AStoker/sound-machine/3d-print/enclosure-wiring.png

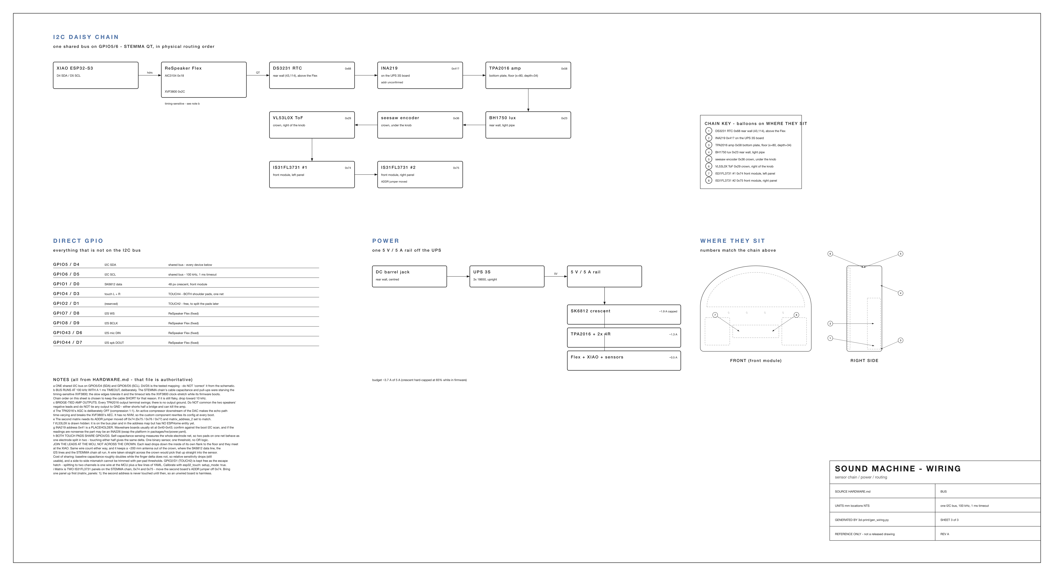
3d-print/enclosure-wiring.png
