AStoker/sound-machine/3d-print/models/backpack-mount-study.png

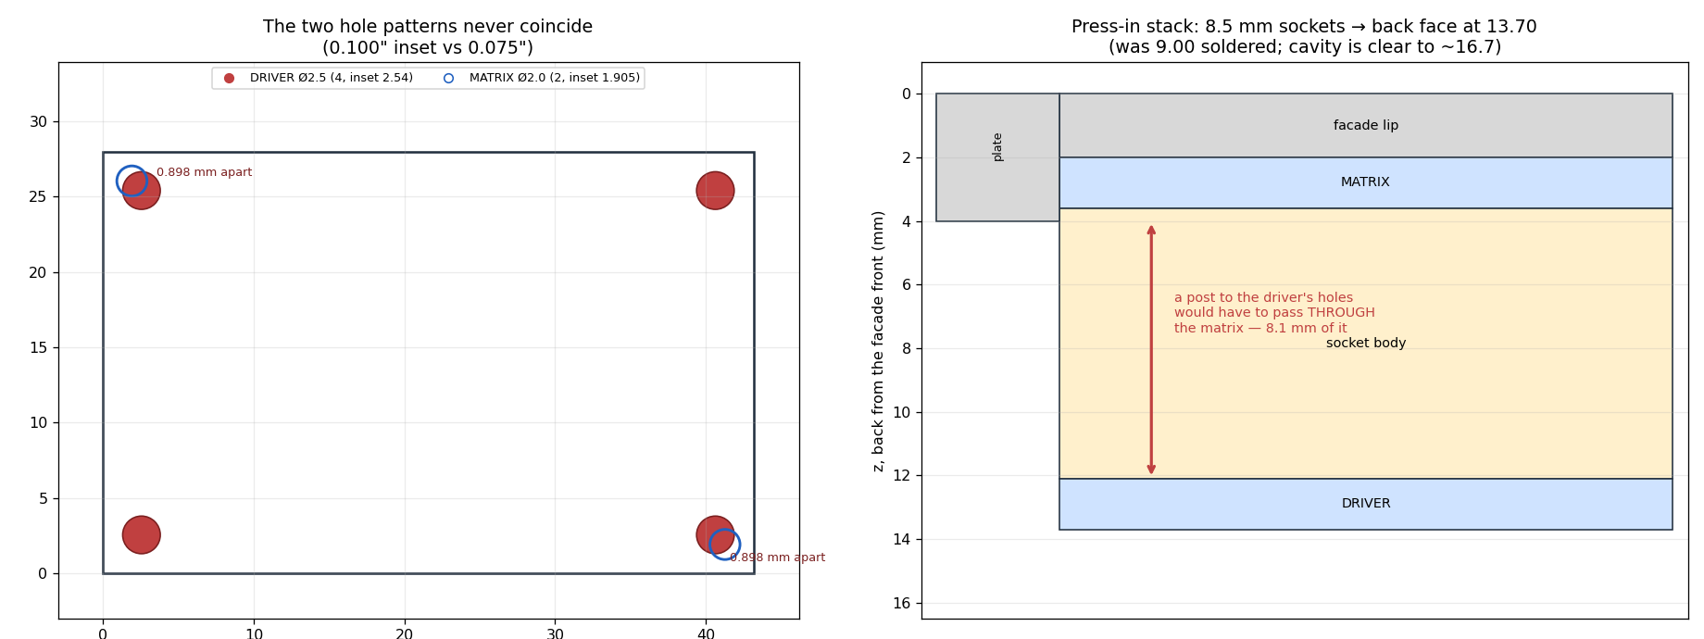
3d-print/models/backpack-mount-study.png
