AStoker/sound-machine/3d-print/models/bottom-plate-check.png

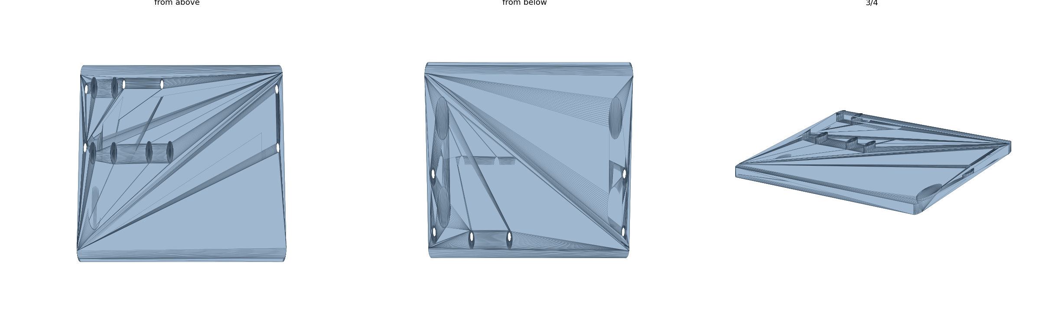
3d-print/models/bottom-plate-check.png
