AStoker/sound-machine/3d-print/models/matrix-mount.png

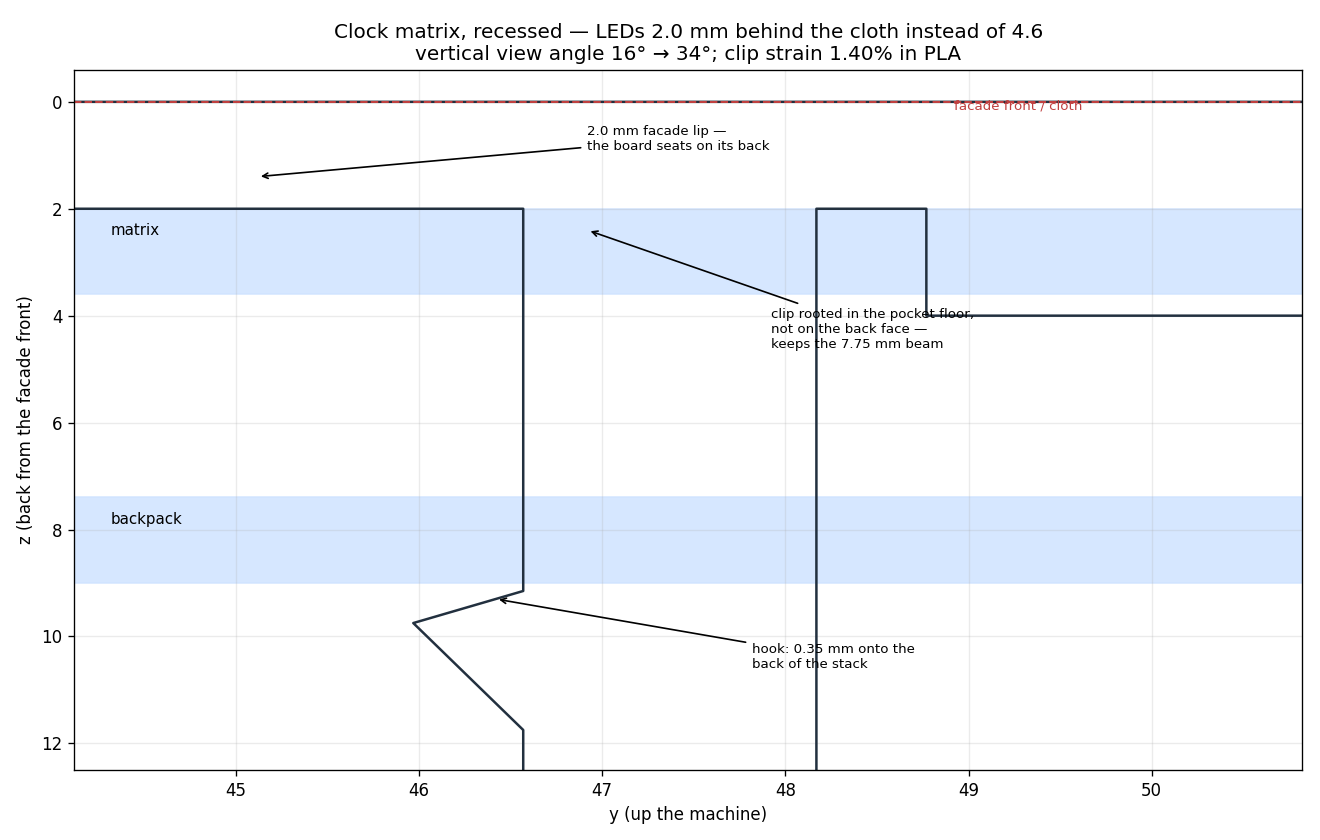
3d-print/models/matrix-mount.png
