AStoker/sound-machine/3d-print/tray_sections.png

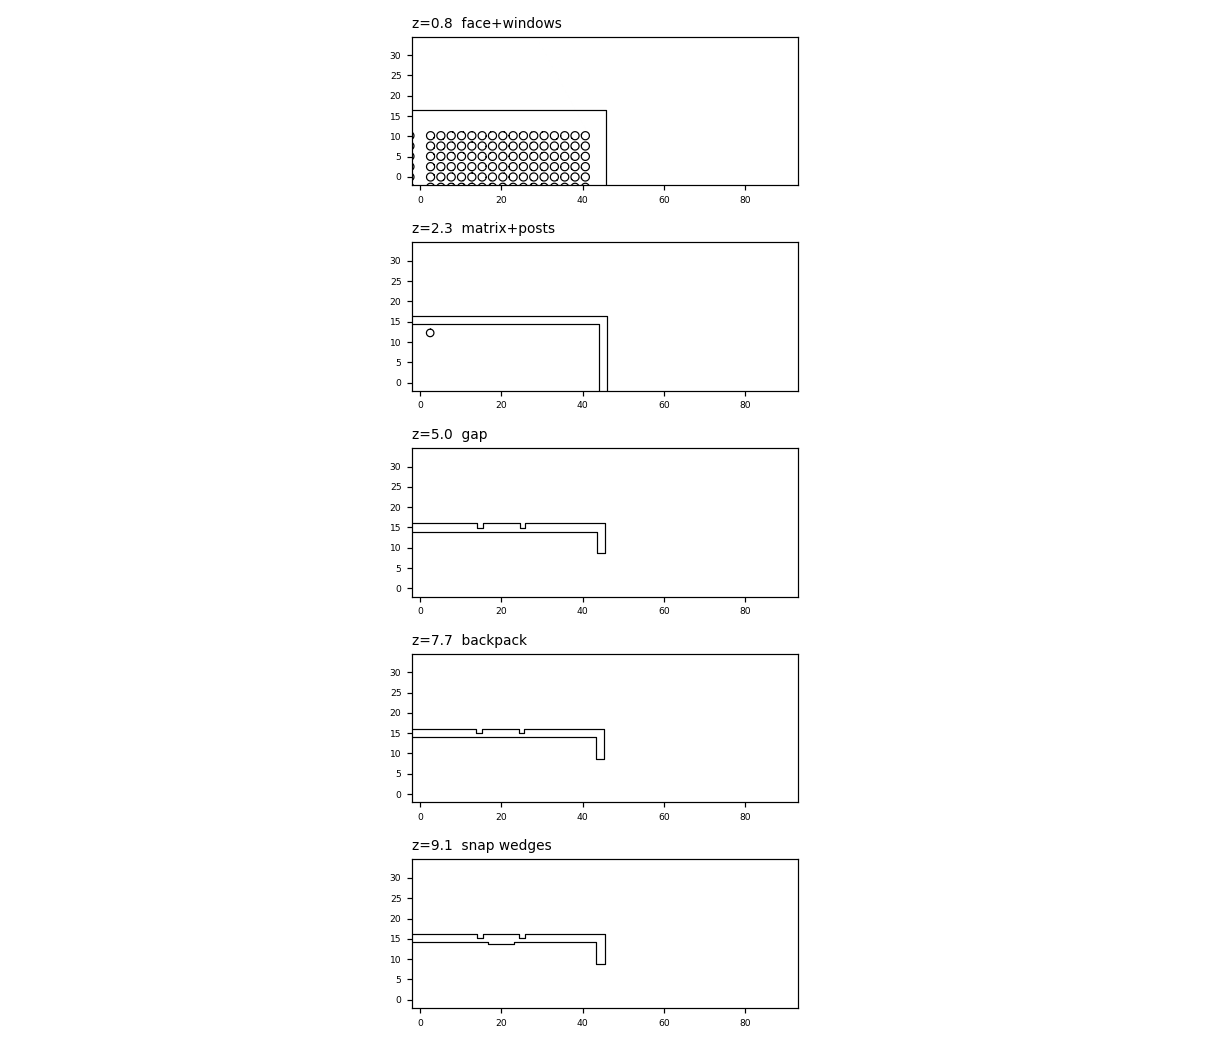
3d-print/tray_sections.png
