AStoker/sound-machine/3d-print/models/matrix-testfit.png

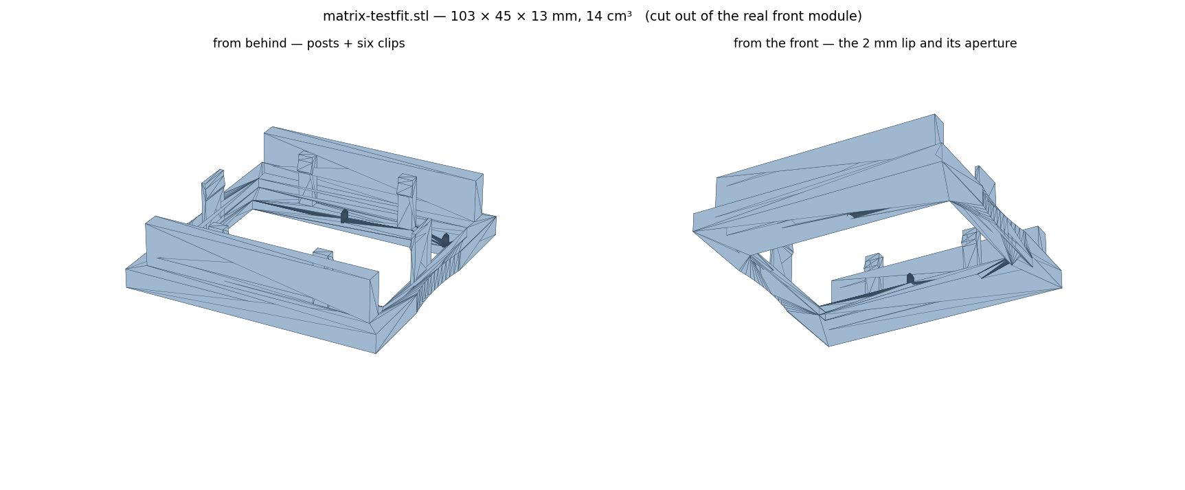
3d-print/models/matrix-testfit.png
