AStoker/sound-machine/3d-print/models/dome-changes.png

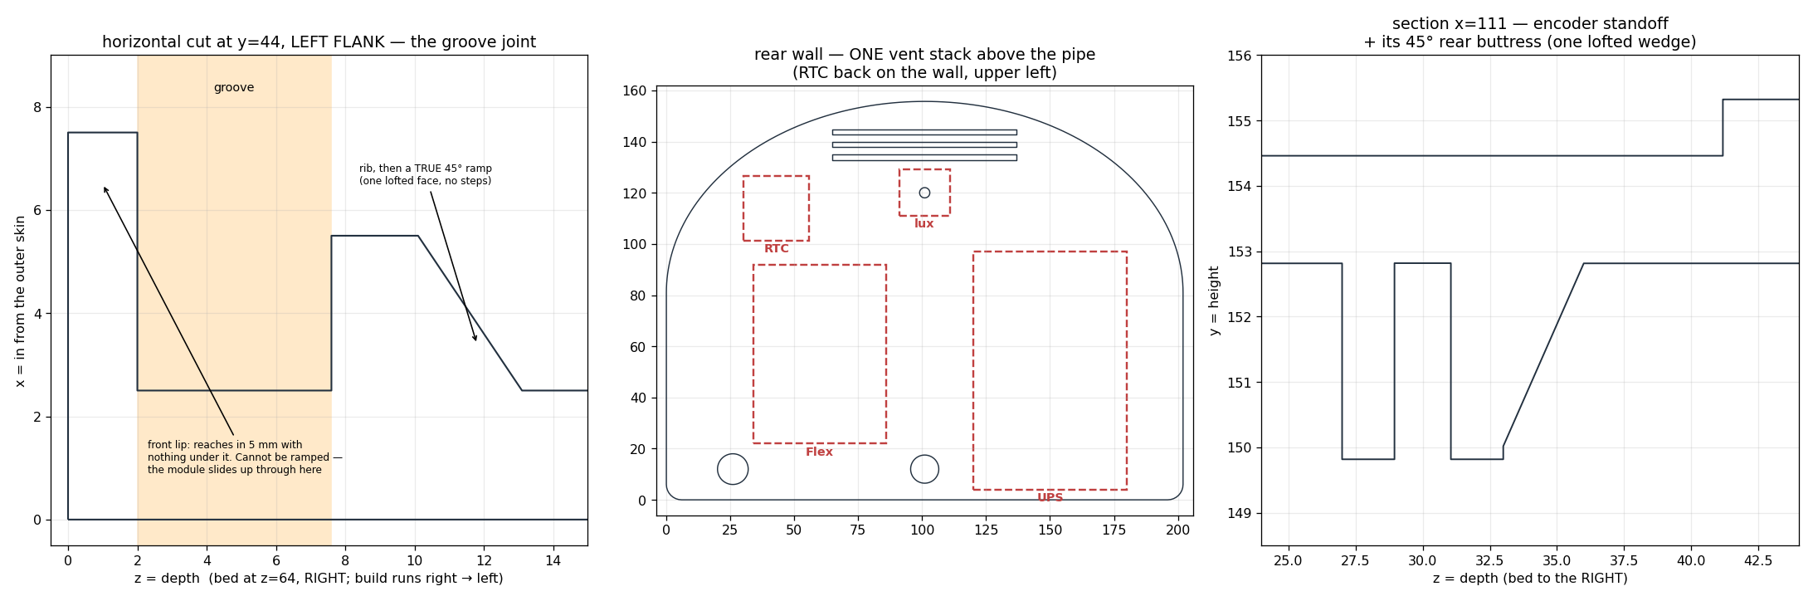
3d-print/models/dome-changes.png
