AStoker/sound-machine/3d-print/models/front-plate-changes.png

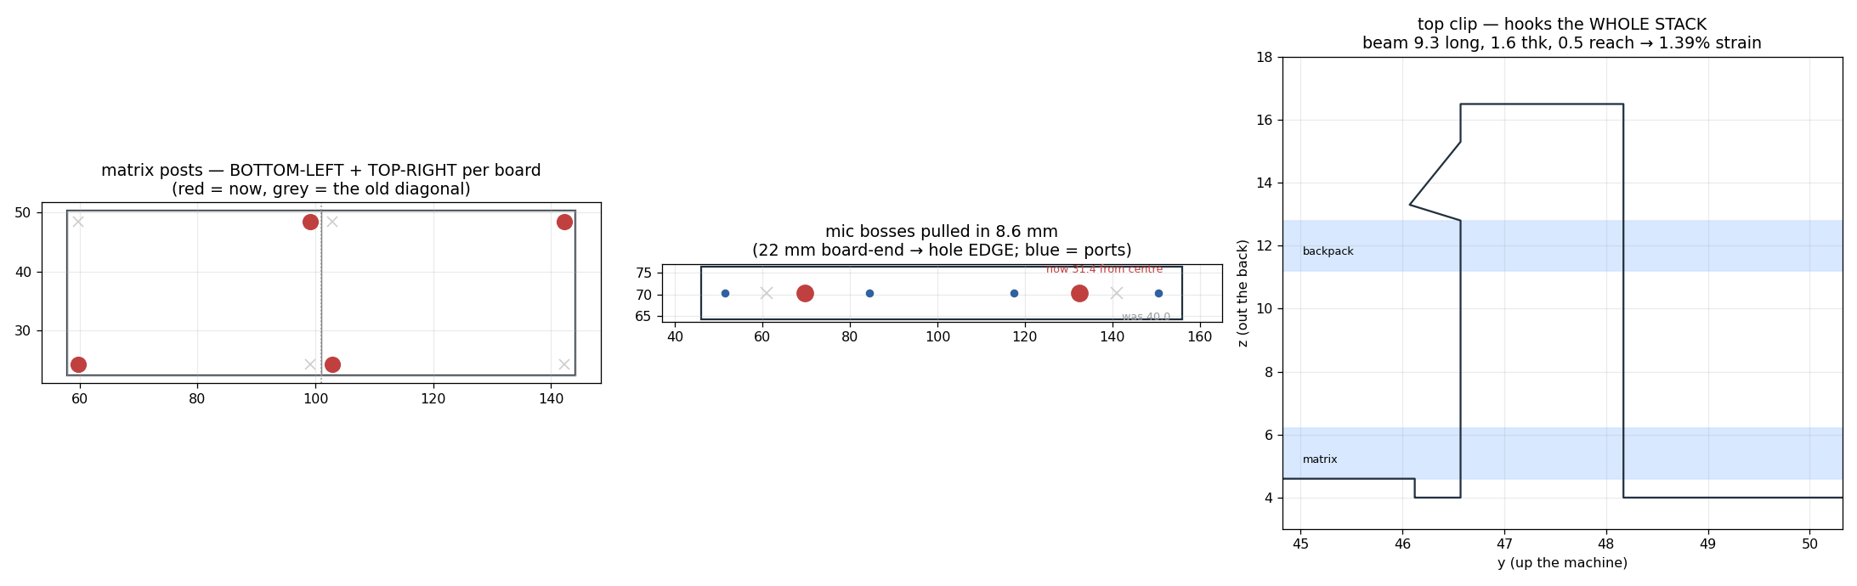
3d-print/models/front-plate-changes.png
