AStoker/sound-machine/packages/settings.yaml

# =====================================================================
# SETTINGS - every tunable in the build, in one file
#
# This package contains NOTHING BUT `substitutions:`. It is the single place to
# change a value; no package below it hardcodes a number you might want to edit.
# It is split out of soundmachine.yaml so the entry file can stay a short,
# readable device core.
#
# HOW THESE ARE OVERRIDDEN. Local substitutions beat package ones, so the tiny
# device YAML on Home Assistant (soundmachine.min.yaml) can override any value
# here - that is how credentials get injected without `!secret` ever appearing in
# this repo (remote ESPHome packages forbid `!secret`).
#
# SECTIONS, in the order the packages that read them are loaded:
#   1. Device identity + credentials
#   2. Buses and pins (I2C addresses, I2S, GPIO)
#   3. Ambient light (the shared auto-dim level)
#   4. Display service (content channels, clock, message widths)
#   5. Clock display (the LED matrix panels)
#   6. Audio chain (amp, noise, volume, ducking, voice)
#   7. Crescent light (strip, presets, sunrise, alarm)
#   8. Knob indicator + proximity
#   9. Power / UPS monitoring
#  10. Gestures (shared tap/hold timings)
#  11. Media sources
#  12. Logging
#
# CONVENTION: a value that is DERIVED from something else (the LED row layout,
# the display panels' register map) is NOT a substitution - it lives next to the
# code that owns it, so nobody is tempted to "tune" it. See the crescent note in
# CLAUDE.md for the one geometry coupling that is enforced by a script.
# =====================================================================
substitutions:

  # ===================================================================
  # 1. DEVICE IDENTITY + CREDENTIALS
  # ===================================================================
  device_name: soundmachine
  device_friendly_name: Sound Machine
  ap_ssid: "Soundmachine Setup"

  # ---- Credentials (injected, NOT stored here) ----
  # This config is designed to be pulled as a remote ESPHome package, and remote
  # packages may not contain `!secret` lookups. So credentials are substitutions
  # instead: the local device YAML on Home Assistant overrides each of these with
  # `!secret ...` from its own secrets.yaml (a local substitution wins over the
  # package's). The values below are PLACEHOLDERS - a real build must override
  # them. See soundmachine.min.yaml / secrets.example.yaml.
  wifi_ssid: "set-in-local-secrets"
  wifi_password: "set-in-local-secrets"
  ap_password: "set-in-local-secrets"
  ota_password: "set-in-local-secrets"
  # Must be a valid 32-byte base64 key or even a bare `esphome config` fails
  # format validation before the local override lands. This is a throwaway key.
  api_key: "kreOUJQZbPUFn1efUReXwEbfhkZzuGGXk1t2AKESiVs="

  # ===================================================================
  # 2. BUSES AND PINS
  # HARDWARE.md holds the authoritative map and the wiring cautions; these are
  # the values the firmware actually uses.
  # ===================================================================

  # ---- I2C: ONE bus, everything hangs off it ----
  pin_i2c_sda: GPIO5                 # D4 on the XIAO/Flex breakout
  pin_i2c_scl: GPIO6                 # D5
  # 100 kHz, not the 400 kHz default: slower edges tolerate the extra cable
  # capacitance and pull-ups of the STEMMA sensor chain, which was starving the
  # timing-sensitive XVF3800. If it is still flaky with everything reconnected,
  # try 10kHz. EVERY package that adds I2C traffic is written to respect how
  # narrow this bus is - see the knob indicator and the display dedup.
  i2c_frequency: 100kHz
  # Room for the XVF3800 to clock-stretch while its firmware boots; without it
  # setup logs "I2C transaction timeout".
  i2c_timeout: 1ms

  # ---- I2C addresses (no conflicts; confirm against the boot scan) ----
  i2c_addr_codec: "0x18"             # AIC3104 codec on the Flex
  i2c_addr_ambient_light: "0x23"     # BH1750
  i2c_addr_tof: "0x29"               # VL53L0X
  i2c_addr_xvf3800: "0x2C"           # ReSpeaker XVF3800 voice front-end
  i2c_addr_knob: "0x36"              # rotary encoder + its NeoPixel
  i2c_addr_amp: "0x58"               # TPA2016 amplifier
  i2c_addr_rtc: "0x68"               # DS3231 real-time clock

  # ---- I2S (pins fixed by the Flex's internal routing - do not change) ----
  pin_i2s_ws: GPIO7                  # D8, LRCLK
  pin_i2s_bclk: GPIO8                # D9
  pin_i2s_din: GPIO43                # D6, mic data in
  pin_i2s_dout: GPIO44               # D7, speaker data out

  # ---- Remaining GPIO ----
  pin_crescent_data: GPIO1           # D0, SK6812 data. Verify D0 is exposed and
                                     # unused on the Flex breakout pads.
  touch_pin: GPIO4                   # capacitive preset pad (D3; D2 = GPIO3).
                                     # ESP32-S3 touch channels are GPIO1..14.

  # ===================================================================
  # 3. AMBIENT LIGHT - the shared auto-dim level
  # The BH1750 produces ONE abstract level, 0..15 (`ambient_level`), consumed by
  # both the display service and the knob indicator. Deliberately weighted dark:
  # the level sits at the floor for anything up to a dim room and only climbs
  # into the top half in real daylight, because this device is 60cm from a face
  # at 3am.
  # ===================================================================
  ambient_update_interval: 5s
  ambient_lux_dark: "3"              # at/below this lux -> ambient_level_min
  ambient_lux_bright: "500"          # at/above this lux -> ambient_level_max
  ambient_level_min: "0"             # floor of the scale; the matrix maps this
                                     # onto matrix_pwm_min, never to fully dark
  ambient_level_max: "14"
  # Curve shape between the two anchors. >1 holds the low end down; 1.0 would be
  # a straight log ramp, which leaves an ordinary lamp-lit room too bright.
  ambient_dim_gamma: "1.8"
  # Per-reading slew toward the target level (0..1). Stops a visible step when
  # someone walks past the sensor. 1.0 = snap.
  ambient_slew: "0.35"

  # ===================================================================
  # 4. DISPLAY SERVICE (packages/api/display.yaml)
  # What gets SHOWN and for how long. How it is drawn is section 5.
  # ===================================================================
  # One heartbeat drives everything the display does: expiring timed overlays,
  # advancing a scroll, and picking up the minute rolling over. It is safe to
  # tick this fast because the driver skips the I2C write when the resolved frame
  # is unchanged - an idle tick costs building a small struct and comparing it.
  display_tick_ms: "250"
  clock_24h_mode: "false"            # true = 24h; the leading zero is blanked
                                     # either way

  # How long a transient CODE ("L1", "S3", "OFF", a volume percentage) stays up.
  display_code_seconds: "2"

  # ---- KEEP THE STRINGS BELOW TO 4 CHARACTERS ----
  # 4 is how many glyphs fit on this display without one of them landing on the
  # dead column between the two panels, so 4 characters is what SITS STILL.
  # Longer strings still work, they just scroll - and a scrolling pass takes far
  # longer than the few seconds one of these is meant to occupy. The budget is the
  # same for every channel, because every channel is drawn the same way; the
  # slot layout is explained in components/clock_display/clock_display.h under
  # "STATIC TEXT NEVER TOUCHES THE SEAM".
  #
  # Power-source announcements, raised when External Power flips (charger in or
  # out). Gated on the averaging window plus ups_confirm_time, so the message
  # lands up to ~90s after the plug moves, not instantly - that lag is what
  # stops a full pack's idle current excursions announcing a false mains loss.
  power_msg_mains: "CHG"
  power_msg_battery: "BATT"
  power_msg_seconds: "3"
  # The sticky low-battery alert. It is a DEFAULT VIEW, not an interruption: it
  # stands in for the clock while the pack is low and anything transient - a
  # volume readout, a preset code, "CHG" - still shows over the top of it.
  # Short and STATIC on purpose: this one persists for as long as the pack is
  # low, and a permanently scrolling word at a bedside at night is worse than no
  # warning at all.
  alert_msg_low_battery: "LOW"

  # ---- Home Assistant authored message (packages/behavior/message.yaml) ----
  display_message_duration_default: "20"  # seconds the custom text stays up
  display_message_duration_min: "3"
  display_message_duration_max: "300"
  # Horizontal scroll rate, used for any text too wide for its channel's budget.
  display_scroll_ms_per_px_default: "250"  # lower = faster
  display_scroll_ms_per_px_min: "30"
  display_scroll_ms_per_px_max: "1000"
  display_scroll_ms_per_px_step: "10"

  # ===================================================================
  # 5. CLOCK DISPLAY - the tiled 16x9 LED matrix panels
  # ===================================================================
  # The panel addresses, left to right. HOW MANY PANELS THERE ARE is not a
  # setting: it is the length of the `addresses:` list in hw/matrix.yaml, so
  # there is nothing here that could disagree with it. To bring up the left panel
  # alone, delete the second entry from that list - the other address is then
  # never touched, so an unwired board causes no I2C errors.
  matrix_address: "0x74"             # panel 0 (left)
  matrix_address_2: "0x75"           # panel 1 (right); set the 2nd board's ADDR
                                     # jumper to a free address (0x75/76/77)
  # Physical dead columns between adjacent panels. Two panels butted together
  # are NOT seamless; the driver lays content out in physical columns that
  # include this gap and maps back to logical columns at draw time.
  matrix_panel_gap: "1"
  matrix_pwm_on: "40"                # lit-pixel PWM at full ambient (0..255)
  matrix_pwm_min: "3"                # lit-pixel PWM floor at the darkest end.
                                     # Never 0 - digits must stay readable.
  # How often the driver checks that the panels still hold the configuration it
  # wrote them. The panels have no NVM, so a glitch on the 5V rail returns them
  # to their power-on state - blanked, with every LED disabled - and they would then
  # sit dark forever while the driver happily kept pushing PWM at them. The probe
  # is a 1-byte register read per panel, so this is cheap to run often; the
  # ceiling on how long a reset display could stay dark is this interval.
  matrix_probe_interval: 10s

  # ===================================================================
  # 6. AUDIO CHAIN
  # ===================================================================
  # The audio stack is not safe to drive until well after setup: starting the
  # noise generator during setup dereferenced an uninitialized event group and
  # crashed. api/sound.yaml waits this long at boot priority -100, then raises
  # on_audio_ready.
  audio_ready_delay: 2s

  # ---- Speaker amplifier ----
  # gain_db is the CEILING, not the operating point - volume lives in the
  # AIC3104 upstream. Was 6 dB (~1W full-scale); raised to 9 dB (~2W) because
  # the mix was a touch quiet. That is near the physical ceiling of a 5V/4-ohm
  # amp (the limiter parks at ~2.5W), so there is little clean headroom left.
  # Going much past 9 pushes normal peaks into the limiter, which distorts AND
  # makes the DAC->speaker path non-linear again - the exact thing running with
  # AGC off is protecting for the XVF3800's echo canceller. If you hear it clip
  # or "breathe" before the knob maxes out, come back down.
  # NOT the lever for the constant speaker hiss - that is the codec's own
  # converter noise, upstream of this gain, so turning it down attenuates hiss
  # and signal equally. Diagnosis and the real options are in
  # FUTURE-DEVELOPMENT T6.
  amp_gain_db: "9"
  # 9.0 dBV is the top of the range (~2.5W into 4 ohm), just under the clipping
  # point at 5V. It should NEVER engage in normal use - it is a fault stop, not
  # a dynamics tool.
  amp_limiter_dbv: "9.0"
  # How often the amp's registers are re-written. The amp has no NVM, so a glitch
  # on the 5V rail returns it to factory defaults - AGC back ON, which quietly
  # breaks the XVF3800's echo canceller and has no other symptom. Four verified
  # register writes, so this is affordable to repeat; the interval is the longest
  # the device could run mis-configured.
  amp_reassert_interval: 60s

  # ---- Noise generator ----
  noise_gain: "30%"                  # base amplitude; leaves headroom so noise
                                     # plus a TTS reply cannot clip
  noise_fade_length: "2s"
  noise_high_pass_hz: "160"
  noise_high_pass_makeup: "4.0"      # tune by ear against white at one volume

  # ---- Sampled ambiences (La La and Crickets; packages/hw/audio_chain.yaml) ----
  # These apply to ALL of them - the component holds one gain and one fade for the
  # whole list, because per-file levelling belongs in the files. 100% because each
  # FILE already carries its own level (see section 11), and at unity the
  # component passes decoded frames through untouched. Re-encode rather than
  # turning this down: the peak headroom the mixer and a TTS reply need was
  # chosen per file, and one gain here cannot respect two different ceilings.
  ambience_gain: "100%"
  # Applied when an ambience starts, and when one is switched for another. Shorter
  # than the noise fade because there is no cold filter state to ease in - the
  # first sample is already the right sound. There is deliberately NO fade at the
  # loop point.
  ambience_fade_length: "1s"

  # ---- Volume ----
  #
  # THE VOLUME FRACTION IS LINEAR IN DECIBELS, WHICH IS WHY THESE NUMBERS LOOK
  # THE WAY THEY DO. Follow one knob click through the chain: the media player
  # remaps its 0..1 volume into [volume_floor_pct, volume_ceiling_pct], hands
  # that to the mixer, which hands it to the AIC3104, whose DAC volume register
  # is 128 steps of 0.5 dB (0x00 = 0 dB, 0x7F = -63.5 dB, 0x80 = mute). So
  #
  #     attenuation = 64 dB x (1 - floor) x (1 - knob)
  #
  # and the knob fraction is already a perceptual scale - equal fractions of the
  # knob are equal decibels. Two things follow, and both were wrong before:
  #   * The FLOOR sets how quiet the machine can get, in dB, and nothing else
  #     does. At the old 55% the bottom of the knob was only -28.8 dB, which is
  #     a bedroom-at-2am kind of loud for a hot recording like Crickets.
  #   * A step curve that is COARSE at the bottom (the old one, ~9% per click
  #     there) spends 2.6 dB on a click at exactly the level where you are
  #     trying to place a whisper. Fine steps belong at the quiet end.
  volume_floor_pct: "30%"            # media_player volume_min. Bottom of the
                                     # knob = -44.8 dB, i.e. 16 dB quieter than
                                     # the old 55%; a true whisper is reachable.
                                     # Knob EXACTLY 0 still mutes the codec
                                     # outright (media player mutes below 0.001),
                                     # which is also the one setting with no hiss
                                     # (FUTURE-DEVELOPMENT T6).
                                     # LOWER STILL IS NOT FREE: the codec's hiss
                                     # does not scale with volume, so every dB of
                                     # extra range makes it relatively louder at
                                     # the bottom. If the quiet end sounds hissy
                                     # rather than quiet, come back up, don't
                                     # chase it with amp_gain_db.
  volume_ceiling_pct: "100%"
  # Knob step curve, interpolated across the knob's travel:
  #     step = at_zero + (at_full - at_zero) x volume
  # FINE WHEN QUIET, coarse when loud - the opposite of what was here before,
  # because the fraction is decibels (above) and the quiet end is the end that
  # gets used. ~1.1 dB per click near the bottom, ~2.7 dB near the top, and
  # ~25 clicks for the full sweep - close to the ~21 it used to take, so the
  # knob has not become a longer journey, only a better-placed one.
  volume_step_at_zero: "0.025"
  volume_step_at_full: "0.06"

  # ---- Voice assistant + ducking ----
  wake_word_model: okay_nabu
  # 0.9, down from the 0.97 default: a bit more forgiving, especially once
  # background sound resumes after a turn.
  wake_word_cutoff: "0.9"
  mic_mute_update_interval: 60s      # was 1s - quieter logs, still functional
  duck_decibels: "15"                # dip applied to background sound for a turn
  # In MILLISECONDS, not a time period: these are passed as script parameters
  # (see sound_duck_apply in api/sound.yaml, which writes the channel list once
  # rather than once per depth), and a script parameter is a plain int.
  duck_ramp_ms: "300"                # ramp INTO the dip
  unduck_ramp_ms: "500"              # ramp back out - gentler, so the background
                                     # does not swell after a reply
  # The duck watchdog waits for the spoken reply to start, then to finish. Both
  # waits are bounded so a stuck announcement state cannot leave sound ducked
  # forever.
  duck_reply_start_timeout: 10s
  duck_reply_end_timeout: 30s

  # ===================================================================
  # 7. CRESCENT LIGHT - SK6812 strip, presets, sunrise, alarm
  # NOTE: the pixel COUNT and row layout are NOT here. They are derived from the
  # enclosure geometry and live in packages/hw/crescent.yaml, checked by
  # 3d-print/check_docs.py. See the coupling note in CLAUDE.md.
  # ===================================================================
  # Gamma 1.0 = linear brightness, so low values still light. SK6812s otherwise
  # blank out below ~20% at the default 2.8 gamma. Raise toward 2.8 for a more
  # perceptual fade, at the cost of the dim end.
  led_gamma: "1.0"
  # Hard current ceiling, as a % of full-white output. Caps max PWM
  # (color_correct) so the strip PHYSICALLY cannot exceed it whatever HA asks.
  # BUDGET (5V rail = Waveshare UPS 3S, 5A):
  #   48 SK6812 RGBW at full all-channel white ~= 2.9A
  #   Speaker amp into 2x 4ohm at clipping           ~= 1.3A
  #   Flex + XVF3800 + ESP32-S3 + sensors        ~= 0.5A
  # STOPGAP: 65% (~1.9A, ~3.7A of 5A total on paper) was enough to brown out the
  # ESP32 in practice - the strip latches its last frame independent of the MCU,
  # so once the rail sags enough to reset the ESP32 it can't recover: the LEDs
  # keep drawing the same current through the reboot loop. Real fix is bulk
  # capacitance at the strip + ESP32 5V inputs and verifying the wiring/feed
  # topology (see HARDWARE.md); this cap is just a stopgap until that's done.
  # THAT HARDWARE FIX IS STILL OUTSTANDING - tracked as the hardware TODO in
  # SOUNDMACHINE.md section 4. Until it lands this value is a SAFETY LIMIT, not a
  # brightness preference: raising it can put the device in a reboot loop it
  # cannot exit on its own (the strip latches its frame independently of the MCU).
  # 25% of 2.9A = ~0.73A for the strip, ~2.5A of 5A total. Raise only after the
  # hardware fix, and only in small steps while watching for the same failure.
  led_max_pct: "25%"
  crescent_transition: 3s            # slower ramp -> gentler current step

  # ---- Static presets ----
  # A second brightness layer on top of led_max_pct: cap what a preset may
  # command so nothing even approaches the current ceiling. Fractions (0..1).
  nightlight_brightness: "0.12"      # deep amber, minimum useful glow
  nightlight_red: "1.0"
  nightlight_green: "0.30"
  nightlight_blue: "0.0"
  morning_brightness: "0.60"         # the brightest STATIC preset
  morning_red: "1.0"
  morning_green: "0.55"
  morning_blue: "0.15"
  # NOTE: there is no preset COUNT here. How many presets the tap gesture cycles
  # is derived from the Crescent Preset select's own option list in
  # packages/behavior/light.yaml - see the CONVENTION note at the top of this file.

  # ---- Circadian Sunrise (the wake-up preset) ----
  # The effect's name, shared so that hw/crescent.yaml (which declares the effect)
  # and behavior/light.yaml (which asks for it by name) cannot drift apart. A
  # mismatch would otherwise be a silent runtime no-op, not a build error. Same
  # applies to the two effect names further down.
  sunrise_effect_name: "Circadian Sunrise"
  sunrise_default_minutes: "30"      # dawn ramp length. 30 min is the typical
                                     # dawn-simulation protocol in the research.
  sunrise_default_hold: "10"         # bright hold, in minutes, before auto-off
  sunrise_max_brightness: "0.70"     # caps the sunrise's peak output
  sunrise_update_interval: 100ms     # effect repaint rate
  sunrise_edge_softness: "0.15"      # vertical width of the sun's glowing edge,
                                     # as a fraction of the crescent's height

  # ---- Colour Cycle + Rainbow Arch (the two ambient effects) ----
  # Both are EFFECTS rather than static colours, because one paints over time and
  # the other paints per pixel. Their brightness is a setting for a reason worth
  # knowing: an addressable light stops applying its own brightness to pixels a
  # running effect owns, so the Home Assistant slider does nothing while either
  # of these is on and the number below is the only control there is.
  #
  # ON CURRENT: neither is a brightness risk, despite looking bright. A fully
  # saturated hue lights at most two of the strip's four channels, so at 0.50
  # these draw roughly (2/4 x 0.50) of the full-white figure the led_max_pct
  # budget is written against - less than Morning Light, which lights three. And
  # led_max_pct caps the lot regardless. See section 7's budget note.
  cycle_effect_name: "Colour Cycle"
  cycle_period_s: "180"              # seconds for one full trip round the hue
                                     # wheel. 3 min is slow enough that the
                                     # colour never appears to be moving.
  # Repaint rate. This one is not just "often enough to look continuous": with
  # the dithering below, the crescent's AVERAGE colour advances in 1/48ths of an
  # output step, and a frame is the only chance it gets to move. At 20 Hz it
  # advances ~2 of those per frame; at 10 Hz it was ~5, which is visible as
  # micro-stepping even with the dither doing its job. 48 pixels of RMT at 20 Hz
  # is ~3% duty on a peripheral nothing else uses.
  cycle_update_interval: 50ms
  cycle_brightness: "0.50"           # ALSO A RESOLUTION KNOB - see below. 1.0
                                     # would double the number of levels the
                                     # colour is rendered in (and the draw).
  # How far apart in HUE the two ends of the crescent are, in degrees, so the
  # pixels straddle an output quantisation step instead of all crossing it at
  # once. The full rationale is in hw/crescent.yaml; the sizing rule is:
  #
  #     one output step = 60 / (255 x cycle_brightness x led_max_pct) degrees
  #                     = 60 / 32 = ~1.9 at the current settings
  #
  # 3 degrees is a shade over one step, which is the safe direction to err: too
  # small and the dither stops working, too large just means the crescent holds a
  # few degrees of hue spread - and 3 degrees of hue is not something the eye
  # picks out as a gradient. Raise it if you raise led_max_pct or the brightness.
  cycle_pixel_spread_deg: "3.0"
  rainbow_effect_name: "Rainbow Arch"
  rainbow_update_interval: 500ms     # nothing animates - this is just a lazy
                                     # repaint so the frame cannot be left stale
  rainbow_brightness: "0.50"
  # Hue degrees from the outermost band to the centre of the flat edge: 0 (red)
  # to 270 (violet), which is a real rainbow's span. A full 360 wraps back to red
  # and puts two red bands on the arch. KEEP THE DECIMAL POINT - this is pasted
  # straight into a C++ float literal, and "270f" is a compile error where
  # "270.0f" is not.
  rainbow_hue_span: "270.0"

  # ---- Alarm (starts the Sunrise preset) ----
  alarm_default_time: "06:30:00"

  # ---- Capacitive touch pad ----
  # ON THE ESP32-S3 THE THRESHOLD IS A *DELTA*, NOT A RAW COUNT. The S3's touch
  # peripheral (v2) keeps a rolling `benchmark` per channel and fires when
  # (value - benchmark) exceeds the threshold. So the number below is the size of
  # the finger's effect, typically HUNDREDS to a few thousand - not the ~10^5-ish
  # raw reading. (The old ESP32 v1 semantics were an absolute count, which is
  # where the previous 700000 came from; on the S3 nothing can ever exceed it,
  # so the pad could never fire.)
  #
  # MEASUREMENT DURATION MUST BE SET EXPLICITLY - the ESPHome default rails the
  # counter. On v2 the raw reading is the number of clock ticks taken to complete
  # `charge_times` charge/discharge cycles, so it scales LINEARLY with that count.
  # ESPHome derives it as round(measurement_duration_us * 65535/8192), and its own
  # schema default of 8192us therefore yields charge_times = 65535 - the maximum -
  # against a driver default of 500. Any real electrode then overflows the 22-bit
  # counter and every reading pins at 4194303 (0x3FFFFF), benchmark follows it
  # there, and `difference` is permanently 0: the pad can never fire. 63us maps
  # back to 504, i.e. the intended default.
  touch_measurement_duration: 63us   # -> charge_times 504. LOWER this (halve it)
                                     # if the untouched `value` still sits near
                                     # 4194303; raise it for more resolution.
                                     # MEASURED: baseline lands at ~47,500, only
                                     # 1.1% of the 4,194,303 ceiling - so there is
                                     # ~80x of headroom in hand. Since value AND
                                     # delta both scale linearly with this, raising
                                     # it is the lever if the smaller production
                                     # pads behind the thinned wall give too weak
                                     # a delta to separate from noise.
  touch_setup_mode: "false"          # true = log value/benchmark/difference for
                                     # this pad every 250 ms at DEBUG. Flip back
                                     # to false once the threshold below is set.
  # CALIBRATED 2026-08-11 against a 76 x 76 mm bench pad behind the unthinned
  # 2.5 mm dome wall (baseline value ~47,500, well clear of the counter ceiling).
  # Measured over 64 untouched samples and 5 presses:
  #   untouched  mean -12, sd 34, worst positive excursion +50
  #   pressed    per-press medians 6363 / 7465 / 7754 / 12153 / 12731
  # That is a 127x separation, so the exact number is not delicate. 2500 sits
  # 50x above the noise ceiling and 2.5x below the weakest press - biased HIGH
  # within that gap on purpose: the risks this pad actually has are a hovering
  # hand and gripping the dome to move it (both give intermediate deltas that
  # this bench data does not sample), not a missed press.
  # RE-CALIBRATE when the real 40 x 22 pads go in behind the thinned 1.6 mm wall
  # - a smaller pad at a shorter dielectric distance moves both numbers.
  touch_threshold: "2500"
  touch_debounce: 40ms

  # ===================================================================
  # 8. KNOB INDICATOR + PROXIMITY
  # ===================================================================
  # ---- The NeoPixel inside the rotary encoder ----
  # Colour = volume (blue quiet -> green mid -> red loud), lit by turning the
  # knob and pre-lit by the ToF sensor.
  # The PIN is a SEESAW GPIO, not an ESP one: 6 on the Adafruit I2C QT Rotary
  # Encoder (#4991 - the same board whose switch is on its GPIO 24). Other knob
  # boards differ; check the pinout.
  knob_led_pin: "6"
  knob_switch_pin: "24"              # board GPIO for the encoder's push switch
  # Largest detent change one reading may claim before hw/knob.yaml treats it as
  # a glitch rather than a turn. The encoder is read every main-loop iteration,
  # so a real hand cannot fit 12 detents (half a revolution) between two of them;
  # a jump that big is a corrupted position, and acting on it throws the volume
  # at a rail. Rejecting one re-seeds the baseline silently, so the cost of being
  # wrong is a single missed flick, not a stuck reading.
  knob_max_clicks_per_read: "12"
  knob_led_fade_ms: "50"             # fade tick = 20 Hz. This is also the HARD
                                     # ceiling on how often the pixel is written
                                     # over I2C - do not raise it much (see the
                                     # rationale in packages/api/indicator.yaml).
  knob_led_hold_ms: "1500"           # stay at full this long after the LAST
                                     # volume change, then start fading
  knob_led_rise_active_ms: "120"     # knob turn -> essentially instant
  knob_led_rise_near_ms: "700"       # hand approaches -> ease it on gently
  knob_led_fade_out_ms: "1400"       # gradual fade to black once done
  knob_led_near_level: "0.45"        # ToF pre-illumination level (0..1) - a
                                     # findable glow, clearly below "in use"
  # Brightness ceiling, as a fraction of full pixel output, at the two ends of
  # the shared ambient auto-dim. Deliberately low at the dark end: this pixel is
  # at arm's length in a bedroom.
  knob_led_min: "0.10"               # darkest room
  knob_led_max: "0.60"               # daylight
  knob_led_gamma: "1.8"              # >1 = perceptually even fade

  # ---- VL53L0X time-of-flight (knob pre-illumination) ----
  #
  # >>> READ hw/proximity.yaml's header BEFORE CHANGING ANY OF THIS. The sensor
  # >>> does not measure the room in this enclosure - it ranges its own 3.5mm
  # >>> pinhole at a fixed ~0.024m through optical crosstalk - so the verdict is
  # >>> built on DEVIATION from that constant, and none of the numbers below are
  # >>> distances to a hand. There is no "how far away" to tune here.
  tof_update_interval: "250ms"       # every read is I2C traffic on a bus this
                                     # build keeps deliberately quiet - 4/s is
                                     # plenty responsive for "a hand is coming"
  # Long range drops the signal-rate limit from 0.25 to 0.10 MCPS: a real
  # sensitivity lever, and a pointless one right now. A more sensitive receiver
  # just hears the crosstalk more clearly. Revisit WITH the enclosure fix (H4),
  # along with adding `timing_budget: 50ms` to the sensor - the other lever, and
  # equally pointless until the pinhole is opened up.
  tof_long_range: "false"
  # ---- The deviation thresholds, in METRES OF CHANGE from the baseline ----
  # MEASURED on the assembled machine over ~2 minutes of log:
  #   idle            0.020 - 0.030   (mean 0.0245, sd ~0.0015)
  #   hand arriving   0.036, 0.046    (+0.012, +0.022)
  #   hand held over  0.011 - 0.019   (-0.013 to -0.006)
  #   hand leaving    0.028 - 0.038
  # So the worst idle excursion is ~0.0055 and the weakest hand signal is ~0.006.
  # 0.010 sits nearly 2x above the noise, and asserting needs two of them in a
  # row, which the noise never manages. RAISE THIS FIRST if the pixel lights on
  # its own; lower it if a slow hand is missed.
  tof_deviation_near_m: "0.010"      # |reading - baseline| to assert
  tof_deviation_far_m: "0.006"       # must fall below this to release
  # How fast the baseline follows the quiet-room reading, per sample. At 4
  # samples/s, 0.02 is a ~12s time constant: fast enough to absorb something
  # newly parked over the knob within a minute, far too slow to be dragged by a
  # hand passing through. It only ever learns from samples that already look
  # quiet (see the gate in hw/proximity.yaml), so this is drift tracking only.
  tof_baseline_alpha: "0.02"
  tof_baseline_warmup_samples: "20"  # ~5s of settling before any verdict counts
  tof_max_valid_m: "1.2"             # beyond this the crosstalk return itself was
                                     # lost - not a target, a broken measurement
  tof_confirm_samples: "2"           # consecutive near readings to assert
  # Consecutive far readings to release. 8 = 2s, up from 3 = 0.75s, and the
  # reason is specific: A HAND CROSSES THE BASELINE ON ITS WAY IN. The reading
  # rises to ~0.045 as a hand comes down toward the knob, then falls THROUGH the
  # 0.024 baseline to ~0.013 when the hand is right on top of it - so mid-gesture
  # there are 3-4 consecutive samples with almost zero deviation, which is
  # indistinguishable from an empty room to a test that only looks at |deviation|.
  # At 0.75s that dropped the pixel and re-lit it half a second later; measured
  # in the 20:59:31 gesture of soundmachine-logs-10, and reproduced exactly by
  # replaying that log. 2s bridges the crossing while still telling four separate
  # gestures apart. Raising it further merges gestures that were a second apart.
  tof_release_samples: "8"
  # ---- The floor, and what it is NOT for ----
  # The ESPHome component publishes the range register WITHOUT consulting the
  # range-status byte next to it, so a failed measurement arrives dressed as a
  # distance rather than as a failure. This rejects the bottom of that: a reading
  # at or below 5mm is the chip returning nothing useful.
  #
  # IT IS DELIBERATELY WELL BELOW THE READINGS A HAND PRODUCES. It was briefly
  # 0.05, on the reasoning that the chip's usable minimum is ~30-50mm so anything
  # under it must be junk - which is true of a sensor looking at a room and false
  # of this one, where the normal reading is 0.024 and a hand pushes it to 0.011.
  # At 0.05 every single sample was rejected and the sensor went silent.
  #
  # A rejected reading still PUBLISHES as tof_no_target_m so the entity holds one
  # number meaning "nothing usable" rather than flapping between 'unknown' and a
  # junk distance. tof_no_target_m MUST stay above tof_max_valid_m.
  tof_min_valid_m: "0.005"
  tof_no_target_m: "2.0"
  # How many CONSECUTIVE unusable readings before the debounce stops ignoring
  # them and releases. Ignoring them is right for the odd dropped sample; doing
  # it forever would latch the pixel on if the sensor stopped reporting entirely.
  # At tof_update_interval this is 12 x 250ms = 3s of silence before it gives up.
  tof_invalid_hold_samples: "12"
  # Only publish the entity when the reading actually moved this far. WAS 0.02,
  # WHICH WAS LARGER THAN THE ENTIRE SIGNAL: this sensor idles at 0.024 and a
  # hand moves it by 0.010-0.024, so a 20mm gate published "0.02" a handful of
  # times in ten minutes and never showed a hand at all. That is display-only -
  # the debounce always ran off the raw value and was detecting hands the whole
  # time - but it made the entity look dead, and it is the entity you watch when
  # you are trying to work out whether this thing sees anything.
  # 2mm is comfortably above the sensor's own ~1.5mm noise.
  tof_publish_delta_m: "0.002"
  # Re-send the last value this often even when nothing changed, so the entity's
  # last-updated time means "the sensor is still reporting". Without it a live
  # sensor watching an empty room and a sensor that failed at setup look exactly
  # the same in Home Assistant - both a number that never moves.
  tof_heartbeat: 60s

  # ===================================================================
  # 9. POWER / UPS MONITORING - Waveshare UPS Module 3S (3x 18650 series)
  # ===================================================================
  # UPS Monitoring address on the I2C bus. This is the address of the INA219/INA226 chip on the Waveshare UPS module.
  ups_i2c_address: "0x41"
  # Series shunt on the UPS board. ALSO UNCONFIRMED - 0.01 ohm is the usual
  # value for a 5A-class board. If reported current is 10x off, this is why.
  ups_shunt_ohms: "0.01 ohm"
  ups_max_voltage: 16.0V             # 3S tops out at 12.6V; 16V range covers it
  ups_max_current: 5.0A              # matches the board's 5V/5A output rating

  # How often the monitor is read. Everything downstream (SOC, the EMA, the
  # charge/mains debounce) is derived from this cadence, so keep it well under
  # ups_confirm_time.
  ups_poll_interval: "10s"

  # Pack internal resistance in OHMS, used to recover open-circuit voltage from
  # the loaded bus voltage: V_oc = V_bus - (I x R). 0.20 suits 3x 18650 in
  # series plus wiring. THIS IS THE ONE VALUE WORTH TUNING - watch Battery
  # Compensated Voltage (a diagnostic entity) while a big load starts or stops:
  #   Level DROPS when load applied -> resistance too LOW, raise it
  #   Level RISES when load applied -> too HIGH, lower it
  #   Level barely moves            -> about right
  ups_internal_resistance: "0.20"

  # EMA smoothing on the compensated voltage. 1.0 = no smoothing, lower =
  # steadier but slower to react.
  ups_ema_alpha: "0.2"

  # Charge deadband in AMPS, applied to the INSTANTANEOUS current: above +50mA
  # the cells are genuinely absorbing charge.
  ups_charge_threshold_a: "0.05"

  # Mains-loss deadband in AMPS, applied to the AVERAGED current (see the window
  # below), so it can be small. Anything more negative than this, sustained
  # across the window, means the pack is carrying the load.
  #
  # DO NOT raise this back into the hundreds of mA to reject charger excursions.
  # It was 200mA for exactly that reason and it was wrong: this device's idle
  # draw from an 11-12V pack is roughly 100-180mA, UNDER that deadband, so
  # running on battery read as "Plugged In" forever. Duration, not magnitude, is
  # what separates the two cases - that is the window's job, not this value's.
  ups_discharge_threshold_a: "0.05"

  # How many consecutive current samples the mains detector averages over. At
  # ups_poll_interval this is the averaging window in real time (6 x 10s = 60s).
  #
  # THIS is what rejects a full pack's idle excursions on the charger: a ~180mA
  # blip lasting one sample averages to ~30mA over six and never crosses the
  # deadband, while a genuine mains loss holds every sample and crosses within
  # two or three. Shorter window = faster detection, less excursion rejection.
  ups_current_avg_samples: "6"

  # How long a charge/mains state change must hold AFTER the window before it is
  # believed. Rejects one-off sensor noise; at a 10s poll this is ~3 readings.
  # Worst-case latency on a mains change is window + this, so ~90s.
  ups_confirm_time: "30s"

  # SOC at/below this counts as "low battery". The pack VOLTAGE thresholds are
  # not settings: they are the endpoints of a measured lithium-ion rest-voltage
  # curve, documented next to that curve in packages/hw/power.yaml.
  battery_low_pct: "15"
  # Hysteresis gap, in SOC points, before the low-battery latch clears. Without
  # a gap this chatters every time the sunrise ramps and the pack sags across
  # the threshold.
  battery_low_clear_gap: "10"

  # How often the low-battery alert is RE-DERIVED from the two sensors above.
  # This is NOT how fast the warning appears - it is also refreshed the instant
  # either sensor changes. It is the bound on how long a MISSED change can leave
  # the display disagreeing with them, which on a pack that is already flat and
  # already unplugged would otherwise be indefinite. See behavior/power.yaml.
  power_alert_interval: "30s"

  # ===================================================================
  # 10. GESTURES - shared by the knob switch and the touch pad, so both
  # physical controls feel the same. Read by packages/hw/{knob,touch}.yaml.
  # ===================================================================
  gesture_tap_max: 0.8s              # a press shorter than this is a tap
  gesture_tap_gap: 0.2s              # release must hold this long to count
  gesture_hold_min: 1s               # a press longer than this is a hold

  # ===================================================================
  # 11. MEDIA SOURCES
  # ===================================================================
  # ESPHome resolves a LOCAL `file:` path against the config dir of whatever
  # machine runs the build. When this config is pulled onto Home Assistant as a
  # remote package that dir is HA's, not this repo - so a bare `sounds/...` path
  # would not be found there even though the file lives in the repo. A value
  # starting with http(s):// is instead downloaded at build time, so the URL
  # default just works everywhere. For LOCAL/offline dev with the repo checked
  # out, override these with the repo-relative path: sounds/La-la-sad.mp3
  #
  # >>> THE FILES THEMSELVES ARE DOCUMENTED IN sounds/README.md: the format every
  # >>> flashed sound must meet and why it is not negotiable, the ffmpeg recipe,
  # >>> the app-partition size budget, what is peculiar about each of these two
  # >>> recordings, and how to add a third. None of that is a value you tune, so
  # >>> none of it lives here - these two lines are.
  la_la_sad_source: "https://raw.githubusercontent.com/astoker/sound-machine/main/sounds/La-la-sad.mp3"
  crickets_source: "https://raw.githubusercontent.com/astoker/sound-machine/main/sounds/Crickets.mp3"

  # ===================================================================
  # 12. LOGGING
  # ===================================================================
  log_level: DEBUG                   # drop to INFO once everything is stable
  # The ToF sensor logs every reading. WARN hides that per-reading spam; set to
  # DEBUG to see every distance while fine-tuning (CONFIG keeps just the boot
  # dump).
  #
  # ON DEBUG DELIBERATELY while the proximity sensor is being diagnosed. This is
  # the only place the sensor's RAW behaviour is visible - the entity cannot show
  # it, because every kind of "no reading" is deliberately flattened to one
  # number before it gets there. Four readings a second, each one line:
  #   "Got distance 0.183 m"          a real measurement
  #   "Distance is out of range"      the chip saw >=8190mm: genuinely nothing
  #   neither, ever                   the component failed at setup - look for
  #                                   "setup timeout" or "reference calibration
  #                                   failed" from tag vl53l0x at boot, and for
  #                                   0x29 in the boot I2C scan
  # Put it back to WARN once the question is settled.
  tof_log_level: "WARN"
