AStoker/sound-machine/3d-print/gen_front_plate.py

#!/usr/bin/env python3
"""FRONT MODULE -- the single printed part that carries the whole facade.

One part, four jobs:
  * CRESCENT   through aperture + a rebate the opal acrylic drops into from
               behind + a cavity wall that sets the diffusion air gap, and six
               PADS on the inside of that wall for the LED carrier (gen_led_
               carrier.py) to screw onto
  * CLOCK      ONE OPEN APERTURE (deliberately no per-pixel holes) and the two
               CharliePlex matrices held directly. THE BOARDS ARE ONLY LOOSELY
               SOLDERED TO EACH OTHER, so each is located by its OWN posts and
               the pair is clamped by six cantilever CLIPS, on all four sides
  * SPEAKERS   grille apertures + a POST above and below each body, on its
               vertical centreline, that the speaker's nub bolts to. THE BODIES
               ARE ROTATED 90 DEG, so the nubs are top and bottom and the flanks
               carry nothing at all (no seat rings, no side ribs -- see the note
               at the speaker block). These bodies have no baffle bolt pattern.
  * MIC ARRAY  four ports + a recessed channel for the linear-4 board + a raised
               gasket land per port

Geometry comes from enclosure_geom.py -- this file only adds what a 2D drawing
cannot express (draft, clips, ribs, pilot holes). Nothing here re-derives an
envelope dimension; if a number looks like it belongs to the enclosure, it is
imported.

    PRINT FACE DOWN. Every boss, wall and clip then grows upward off the bed and
    the facade -- the one surface anyone sees -- is the bottom layer.

Needs manifold3d (robust CSG):
    .venv/bin/pip install manifold3d trimesh matplotlib
    .venv/bin/python gen_front_plate.py
Outputs models/front-module.stl (+ section previews beside the code).
"""
import math
import os
import struct

from manifold3d import CrossSection, Manifold

from enclosure_geom import (
    ARCH_R, ARCH_Y, BP_T, CAV_WALL, CLK_H, CLK_W, CLK_Y, CRES_R, CRES_Y,
    DIFF_GAP, DIFF_MARGIN, DIFF_REBATE, DIFF_T, FP_T, H, LED_R, MIC_CHAN_D,
    MIC_GASKET, MIC_PCB_H, MIC_PCB_W, MIC_PORT_D, MIC_Y, MIC_Y0, MIC_Y1,
    MTX_BOARD_H, MTX_BOARD_W, MTX_BP_T, MTX_HOLES, MTX_HOLE_D, MTX_N, MTX_PCB_T,
    MTX_STACK_GAP, ARCH_RY, CRES_RY, LED_RY, CROWN_K, SPK_POST_H, SPK_FLANK,
    BOSS_EDGE, LIP, REVEAL, RIB_W, R_BOT, SPK_BODY_H, SPK_BODY_W, SPK_GRILLE, SPK_NUB_PROJ,
    SPK_NUB_SCREW, SPK_NUB_Y, SPK_NUB_Z, SPK_POST_WALL, SPK_RING_W, SPK_SEAT_W,
    SPK_NUB_H, SPK_NUB_W, SPK_POST_W, SPK_POST_H_Y, CLR_POST_MIC,
    DIFF_LIP, CAV_Z, CARRIER_Z0, CARRIER_T, LED_STRIP_T, DIFF_R_G, CAV_RY_G,
    strip_rects, BAFFLE_DROP, CARRIER_SKIRT, CARRIER_LIP, CARRIER_T,
    CARRIER_SCREW_H, CAV_R_G, CAV_RY_G,
    crown_boards, crown_inner_y, CROWN_CLR,
    PAD_PROJ, PAD_W, PAD_DRAFT, PAD_Z0, PAD_RAMP, PAD_OFFSET_IN, PAD_PILOT_D,
    PAD_PILOT_Z, carrier_pads, DIFF_RY_G,
    pad_led_clearances,
    pad_wall_margins, MODEL_DIR, HERE,
    SPK_FIT, SPK_X, SPK_Y, SPK_Y0, SPK_Y1, TRAY_D, TRAY_H, TRAY_REBATE, TRAY_W, TRAY_Y0,
    TRAY_Y1, W, mic_x,
    MTX_WINDOW, MTX_LED_PITCH, MTX_LED_COLS, MTX_LED_ROWS, mtx_led_xy,
)

SEG = 96              # facets on the big arcs -- this part is 245 mm wide
# ---------------------------------------------------------------------------
# PRINT PARAMETERS -- the things a drawing does not fix. Tune these, not the
# imported geometry.
# ---------------------------------------------------------------------------
# DIFF_LIP and CAV_Z are IMPORTED now, not defined here. The LED carrier derives
# its z origin from the same stack, and two files each deriving a z stack from a
# constant only one of them owns is exactly how the earlier drift bugs started.
DIFF_R      = CRES_R + DIFF_MARGIN                 # acrylic pocket, across
DIFF_RY     = CRES_RY + DIFF_MARGIN                #      "        , up
CAV_R       = DIFF_R + CAV_WALL                    # cavity outer wall, across
CAV_RY      = DIFF_RY + CAV_WALL                   #      "            , up
assert abs(DIFF_R - DIFF_R_G) < 1e-9 and abs(CAV_RY - CAV_RY_G) < 1e-9, \
    "cavity ellipse disagrees with enclosure_geom -- the carrier will not fit"

# --- the clock: posts locate, clips clamp -----------------------------------
# THE TWO MATRICES ARE ONLY LOOSELY SOLDERED TOGETHER, so the frame cannot treat
# them as one part. Each board gets its OWN pair of locating posts through its
# own diagonal mounting holes; the clips then clamp the pair flat against the
# facade from all four sides. Posts alone would let the boards pivot off the
# face; clips alone would let the soldered joint carry the alignment.
MTX_STANDOFF = 0.0    # retired: the board seats on the facade lip, not on pads
_UNUSED_STANDOFF = 0.6  # was: posts stand the boards off the facade a touch, so they
                      #   seat on defined pads instead of on stray solder
# >>> THE MATRIX IS RECESSED INTO THE FACADE, NOT HUNG OFF ITS BACK FACE.
# >>> It used to seat on the plate's back face, putting the LEDs 4.6 mm behind the
# >>> cloth at the bottom of an open 84 x 23 well. The well is only 1.34 mm wider
# >>> than the LED field vertically, so the top and bottom rows vanished at just
# >>> 16 deg off-axis -- and a bedside clock is a thing you look DOWN at. Nothing
# >>> flagged it because it is not a clearance problem: everything fitted.
# >>> Recessed to MTX_INSET the same rows hold to 34 deg.
# >>>
# >>> The board seats on the BACK OF THE FACADE LIP -- the frame left around the
# >>> aperture -- which overlaps it by 1.18 mm at the sides and 2.47 top and
# >>> bottom, clear of the LED field (2.5 / 3.8 mm in from the board edges). The
# >>> four locating posts land on that same frame; all four are 1.905 mm from a
# >>> horizontal board edge, so all four are under the lip.
# >>> Seating on the lip also retires the standoff pads: the lip IS the datum.
# >>> 1.5, AND PER-PIXEL WINDOWS INSTEAD OF ONE OPEN APERTURE. The single 84 x 23
# >>> hole meant the lip only touched the board round its rim, so the recess could
# >>> not go below ~2 without the seating frame getting silly-thin. With 288
# >>> windows the lip becomes a perforated sheet that supports the board over its
# >>> WHOLE area, and each LED pokes into its own window -- so the lip can be
# >>> thinner, not thicker. 1.5 gives a 31 deg half-angle through a 1.8 window,
# >>> against 34 deg for the open aperture at 2.0: near-identical, with far better
# >>> per-pixel isolation and no light bleeding sideways between digits.
# >>> 1.5 -> 1.3, AND PIN GUTTERS -- WHICH COMPETE FOR THE SAME 1.5 mm. Worth
# >>> being explicit about, because the two requests pull against each other: the
# >>> trimmed header pins stick out of the board's LED-SIDE face, and the only
# >>> material in front of that face is the lip itself. Behind the board is already
# >>> pocket, so a gutter cannot go backward -- it has to be cut FORWARD into the
# >>> lip, out of the same budget the inset is being reduced from.
# >>>
# >>> THE REAL WIN IS BIGGER THAN 1.5 -> 1.3, THOUGH. Today the pins are what the
# >>> board rests on, so the LED plane sits at MTX_INSET + MTX_PIN_H behind the
# >>> facade -- about 2.3 mm, not 1.5. Gutter the pins and the PCB face reaches the
# >>> lip, so the LED plane lands at 1.3. That is 2.3 -> 1.3: the light bleed goes
# >>> away and the viewing angle improves by more than the inset change alone.
# >>> SO THE INSET IS NO LONGER A FREE CHOICE -- IT IS DERIVED. Setting it to 1.3
# >>> by hand and then cutting a 0.95 gutter into it left 0.35 mm of facade, under
# >>> the 0.4 minimum, and the check caught it. Rather than pick a number that
# >>> happens to work, stack the constraint: the facade in front of a gutter must be
# >>> at least MTX_FACADE_MIN, the gutter must swallow the pin, so the inset is the
# >>> sum. Measure the pins shorter and the inset drops on its own.
MTX_PIN_H    = 0.8    # (?) trimmed header pin, above the LED-side PCB face -- MEASURE
MTX_GUTTER_CLR = 0.15 # air over the pin tip, so it never sets the seating height
MTX_GUTTER_D = MTX_PIN_H + MTX_GUTTER_CLR
# >>> THE PERIMETER WALL IS THE SAME WALL AS EVERY OTHER ONE, so it is derived
# >>> from the grid instead of being its own number. This was 0.3 -- a keep-out I
# >>> picked for the gutter without ever comparing it to the web the grid already
# >>> uses (2.54 pitch - 1.8 window = 0.74). The result: 288 cells with 0.74 mm
# >>> walls between them and 0.30 mm walls closing the top and bottom rows. At a
# >>> 0.4 nozzle that is one sub-nozzle trace, so the boundary cells slice as OPEN
# >>> -- the grid visibly stops having joining walls at its edges, which is exactly
# >>> what Andy spotted in the model.
# >>> Tying it to the pitch means the boundary can never again be the odd one out.
MTX_GUTTER_WEB = MTX_LED_PITCH - MTX_WINDOW      # = 0.74, same as every inner web
MTX_PIN_ROW_BAND = (0.5, 1.8)   # where a 0.1" header row sits, from the board edge
# >>> 0.45, NOT 0.4. Two layers at 0.2 is the structural floor, but this is the
# >>> VISIBLE face and PLA at 0.4 glows: a lit display could show two faint bands
# >>> along the top and bottom of the clock. 0.45 is three layers at 0.15 or a
# >>> comfortable two at 0.2, and the strip is only ~2.5 mm wide in the margin
# >>> where there are no LEDs, so what light reaches it is scatter.
MTX_FACADE_MIN = 0.45
MTX_INSET    = round(MTX_GUTTER_D + MTX_FACADE_MIN, 3)   # 1.40 at PIN_H 0.8
# >>> A SOLID PEDESTAL UNDER EACH LOCATING POST, or the post falls off. The posts
# >>> are 1.905 mm from a horizontal board edge -- i.e. INSIDE the gutter band --
# >>> and a post is attached to the part ONLY at its base on the lip. Cut the lip
# >>> out from under it and it becomes a loose cylinder floating in the pocket.
# >>> The existing "connected bodies == 1" check catches exactly that, which is why
# >>> it is worth keeping honest.
MTX_POST_COLLAR = 0.7 # solid lip kept round each post base, per side
# >>> AND THE CLIPS ROOT IN THE POCKET, NOT ON THE BACK FACE. Recessing the board
# >>> moves the hook forward, and a clip still rooted at z=FP_T would lose that
# >>> length from its beam -- 3.05 % strain at a 1.5 mm inset. Rooted at the
# >>> pocket floor, root and hook move together and the strain stops depending on
# >>> the inset at all, which is what makes the inset a free choice.
MTX_CLIP_FLEX = 0.6   # slot behind each clip, so it is not fused to the wall
# >>> ONE NAME FOR THE CLIP'S ROOT, USED BY BOTH THE GEOMETRY AND THE CHECK.
# >>> They were separately written as MTX_INSET in clip() and in the strain
# >>> formula, which means moving the root in the geometry left the check happily
# >>> reporting the old number -- verified by moving it back to FP_T and watching
# >>> the strain check still pass at 1.40 % on a clip that was really at 4.59 %.
# >>> A check that recomputes the design intent instead of reading the design is
# >>> not a check.
CLIP_ROOT_Z = MTX_INSET
MTX_POST_D   = 1.85   # into the O2.0 hole -- locating only, no barb
MTX_POST_TIP = 0.6    # chamfered lead-in cone (self-supporting on FDM)
MTX_PAD_D    = 2.0    # plain seating pad, in the clear margin above/below the
MTX_PAD_EDGE = 1.2    #   LED field -- see the note where they are placed
# --- matrix retaining clips -------------------------------------------------
# >>> THESE WERE UNBUILDABLE, AND NOTHING CHECKED IT. A snap-fit cantilever's
# >>> peak strain is e = 1.5*t*y/L^2 -- thickness times deflection over the SQUARE
# >>> of its free length. The old clip was 2.2 thick, had to deflect 1.2, and was
# >>> rooted only 2.2 mm below its hook: 82 % strain. PLA breaks around 2 %, PETG
# >>> around 4, nylon around 8. It would not have flexed, it would have shattered
# >>> on the first board -- and no check in this file had an opinion about it,
# >>> because every check here is about CLEARANCE and this is about STRESS.
# >>>
# >>> LENGTH IS THE ONLY REAL LEVER, because it is squared. Thinning the beam or
# >>> shortening the reach buys a few tenths; the beam being 2.2 mm long is what
# >>> made it impossible. So the hook now grips the BACK OF THE WHOLE STACK rather
# >>> than the back of the matrix board -- which is what enclosure_geom always
# >>> intended (MTX_CLIP_Z, "clip hook standing behind the backpack", is already
# >>> in the TRAY_D budget) and it makes the beam 8.8 mm instead of 2.2.
# >>> It also clamps the sandwich properly: matrix front on the seating pads,
# >>> clip pushing on the backpack behind, instead of pinching one 1.6 mm board.
# >>>
# >>> PLA, SO THE REACH IS SMALL ON PURPOSE. The hook is retention, not load --
# >>> it stops the stack lifting off four seating pads, and 0.5 mm of overlap on a
# >>> 1.6 mm board edge does that. The check at the end of this file computes the
# >>> strain and fails above PLA's limit.
CLIP_MAT      = "PLA"
CLIP_STRAIN_MAX = 0.015   # 1.5 %: conservative for PLA, which fails near 2 %
# >>> RETUNED WHEN THE STACK WAS MEASURED. At an assumed 8.2 mm stack the beam
# >>> was 9.3 long; the measured stack is 7.0, so it is 8.35 -- and because length
# >>> is SQUARED, losing 1.2 mm of it moves the strain more than any other change
# >>> here. The stack height is not a clearance, it is the lever arm of every clip
# >>> on this part.
# >>>
# >>> ENGAGEMENT IS THE PRIMARY NUMBER, NOT REACH, AND CONFUSING THE TWO COST A
# >>> REAL DEFECT. CLIP_REACH is measured from the BEAM'S INNER FACE, which stands
# >>> CLIP_GAP off the board -- so the hook only actually overlaps the board by
# >>> (REACH - GAP). Setting REACH to 0.4 left 0.15 mm of grip on a 1.6 mm board
# >>> edge, and the check that was supposed to catch it tested REACH, so it
# >>> passed. The deflection needed to assemble is also the ENGAGEMENT, not the
# >>> reach: the hook tip only has to travel back to the board's edge.
# >>> So the engagement is stated, and the reach is derived from it.
CLIP_W      = 6.0     # clip width
CLIP_T      = 1.6     # cantilever thickness -- thin, because PLA
CLIP_GAP    = 0.25    # clip inner face to board edge
CLIP_ENGAGE = 0.35    # ACTUAL overlap onto the stack's back face (22% of 1.6)
CLIP_REACH  = CLIP_ENGAGE + CLIP_GAP   # hook travel from the beam's inner face
CLIP_RUN    = CLIP_REACH               # run == reach -> 45 deg, self-supporting
CLIP_RAMP   = 2.0     # lead-in ramp length
CLIP_TAIL   = 1.2     # material behind the ramp, so the tip is not a knife edge
# >>> A DELIBERATE SLIVER OF CLEARANCE, BECAUSE THE STACK HEIGHT IS NOT OURS.
# >>> The hook sat at exactly BP_ZB -- the nominal back of the stack -- which is a
# >>> zero-tolerance fit against a dimension this project does not control:
# >>> MTX_STACK_GAP is set by whatever header pins are used, and is flagged
# >>> "your own inter-board header pins" in the README. If the real stack is even
# >>> 0.05 mm proud of nominal the clips cannot close over it, and the failure
# >>> looks like a part that just will not go together.
# >>> Biasing the hook 0.15 mm outward means it always closes; the cost is up to
# >>> 0.15 mm of possible rattle, which four seating pads and two locating posts
# >>> per board already stop from mattering. Erring toward "assembles, with a
# >>> hair of play" beats erring toward "does not assemble".
CLIP_STACK_CLR = 0.15

# --- speakers ---------------------------------------------------------------
SPK_RIB_H   = 5.0     # locating rib height off the back face
SPK_PILOT_D = 2.5     # (?) pilot for an M3 self-tapper -- suits PETG/PLA
SPK_PILOT_Z = 5.5     # pilot depth into the 7 mm post
# --- mic array --------------------------------------------------------------
MIC_FIT     = 0.4     # per side, board to channel
# >>> THE ARRAY IS *MEANT* TO STAND OFF THE CHANNEL FLOOR. It seats on four
# >>> raised Ø4.5 lands, one ringing each Ø2.5 port, and touches nothing else --
# >>> so there is a deliberate 0.6 mm gap everywhere except at the ports. That
# >>> looks like a mistake and is the opposite: pressing the whole board flat
# >>> onto the floor would seal nothing, because an FDM floor is not flat, while
# >>> four small rings can be made to seal.
# >>>
# >>> BUT THE SEAL IS A GASKET, NOT THE PLASTIC. Bare printed plastic against a
# >>> PCB leaks through the layer lines, and a leaking port is worse than a long
# >>> one: it lets sound reach the mic by two paths, which is exactly what the
# >>> XVF3800's beamforming and echo canceller assume is not happening. Each land
# >>> needs a thin adhesive foam ring (~1 mm uncompressed, Ø2.5 hole) -- that is
# >>> what MIC_LAND_H is clearance FOR, and why it is 0.6 and not 0.
# >>> WHAT ACTUALLY SETS THE ARRAY'S HEIGHT IS THIS LAND, NOT THE SCREW BOSS.
# >>> The bosses are just posts the M3s thread into; the board SEATS on the four
# >>> gasket lands, so the land height is the whole of the port length above the
# >>> channel floor. Shortening the bosses would do nothing.
# >>> Dropped 0.6 -> 0.3 for thin foam tape (0.3 is roughly a 0.5 mm tape
# >>> compressed), and MIC_CHAN_D deepened 2.0 -> 2.4 to bring the floor forward
# >>> as well. Together the port goes 2.60 -> 1.90 mm, a 27% shorter path from
# >>> pinhole to microphone, which is what the seal wants.
# >>> SET THIS TO YOUR TAPE'S COMPRESSED THICKNESS. Too tall and the tape does not
# >>> touch the board; too short and it is crushed solid and stops sealing.
MIC_LAND_H  = 0.3     # gasket land = compressed thickness of your foam tape
MIC_BOSS_D  = 5.0     # M3 pilot boss beside the channel
# >>> MEASURED, NOT GUESSED, AND DERIVED FROM THE MEASUREMENT RATHER THAN TYPED.
# >>> Seeed does not publish the array's hole positions; 40 mm from centre was a
# >>> guess. The measured figure is the distance from the END of the board to the
# >>> NEAR EDGE of the screw hole, which is what you can actually get a caliper
# >>> on -- so that is what is recorded, and the boss centre is worked out from
# >>> it. Writing the centre directly would bury the +hole-radius step in a
# >>> number nobody could re-check against the board.
MIC_HOLE_EDGE = 22.0  # board END -> NEAR EDGE of its M3 hole -- MEASURED
MIC_HOLE_D    = 3.2   # M3 clearance hole in the array board
MIC_BOSS_X  = MIC_PCB_W / 2 - (MIC_HOLE_EDGE + MIC_HOLE_D / 2)
MIC_PILOT_D = 1.6     # M2 self-tapper -- a THIN screw, as asked
# --- stiffening -------------------------------------------------------------
# >>> A RIB GETS ITS STIFFNESS FROM HEIGHT, NOT FOOTPRINT. These were 5 mm-proud
# >>> PADS filling the whole band between features -- 92 x 6.6 and 92 x 10.9 --
# >>> which is what a stiffener looks like when it is shaped by the space left
# >>> over rather than by the job. Per 10 mm of length a 9 mm solid pad gives
# >>> I = 608 mm^4 for 90 mm^2 of material; a 3 x 9 rib on the same 4 mm plate
# >>> gives I = 917 for 67. Half again the stiffness, a quarter less plastic, and
# >>> it reads as a deliberate feature instead of an unexplained plateau.
# >>> There is room: nothing sits behind either band until the matrix backpack at
# >>> z = 12.8, and that is at a different height entirely.
RIB_H       = 9.0     # stiffening rib height off the back face
RIB_T       = 3.0     # rib thickness, along y

# --- the print seam ---------------------------------------------------------
# The module is 250.8 wide; the target bed is 220. No rotation helps (this is a
# D, so rotating only grows the bounding box) and the 45 deg tilt that does fit
# would stand the facade up on supports. So it splits -- see the long note at
# the split itself for where the seam can and cannot go.
BED       = 220.0     # Flashforge Adventurer 5M Pro
SPLIT_X   = 73.8      # seam, centred in the one usable corridor
LAP_W     = 5.0       # tongue length -- sized to fit that corridor, not chosen
LAP_Z     = FP_T / 2  # the step: front half / back half of a 4 mm plate
LAP_CLR   = 0.25      # clearance on every mating face
PEG_D     = 2.5       # alignment pegs on the lap face
PEG_H     = 1.5
PEG_Y     = [15.0, 30.0, 56.0, 169.0]   # where the seam has material both sides
_L0, _L1  = SPLIT_X - LAP_W / 2, SPLIT_X + LAP_W / 2
# SPLIT ONLY IF IT HAS TO. Rotating the speakers and lifting the mic array took
# the module to 194.8 x 152.4, which fits a 220 bed whole -- so the seam is off.
# It stays in the code because the seam location was hard-won, and any change
# that pushes the part back over the bed turns it on again automatically.
NEEDS_SPLIT = max(W - 2*REVEAL, H - REVEAL - BP_T) > BED

_out = []


def say(s):
    _out.append(s)
    print(s)


# ---------------------------------------------------------------------------
# 2D helpers. Everything is built in DRAWING coordinates -- x 0..W from the
# left, y 0..H measured UP -- so the imported constants drop straight in.
# ---------------------------------------------------------------------------
def poly(pts):
    """CrossSection from a point list, forced counter-clockwise."""
    a = 0.5 * sum(pts[i][0] * pts[(i + 1) % len(pts)][1]
                  - pts[(i + 1) % len(pts)][0] * pts[i][1]
                  for i in range(len(pts)))
    return CrossSection([pts if a > 0 else pts[::-1]])


def rect2(x0, y0, w, h):
    return poly([(x0, y0), (x0 + w, y0), (x0 + w, y0 + h), (x0, y0 + h)])


def disc2(cx, cy, r):
    return CrossSection.circle(r, SEG).translate((cx, cy))


def half_disc(cx, cy, r, skirt=0.0, ry=None):
    """Upper half of an ELLIPSE -- the crescent shape, flat side DOWN at cy.
    The crown is flattened (CROWN_K), so `r` is the horizontal semi-axis and
    `ry` the vertical. `skirt` extends the flat side downward, which is how the
    cavity wall gets a bottom to close against."""
    ry = r if ry is None else ry
    pts = [(cx + r, cy)]
    for i in range(1, SEG):
        t = math.pi * i / SEG
        pts.append((cx + r * math.cos(t), cy + ry * math.sin(t)))
    pts.append((cx - r, cy))
    if skirt > 0:
        pts += [(cx - r, cy - skirt), (cx + r, cy - skirt)]
    return poly(pts)


def outline2():
    """The module outline: a 'D' on its long flat side. Straight flanks, a
    semicircular top of radius ARCH_R-REVEAL concentric with the crescent, and
    a flat bottom that lands on the bottom plate."""
    x0, x1 = REVEAL, W - REVEAL
    yb, ys = BP_T, ARCH_Y
    r, rry = ARCH_R - REVEAL, ARCH_RY - REVEAL
    rb = max(R_BOT - REVEAL, 0.8)          # bottom corners
    pts = [(x0 + rb, yb)]
    for i in range(9):                     # bottom-right corner
        t = -math.pi / 2 + (math.pi / 2) * i / 8
        pts.append((x1 - rb + rb * math.cos(t), yb + rb + rb * math.sin(t)))
    pts.append((x1, ys))
    for i in range(1, SEG):                # the arc
        t = math.pi * i / SEG
        pts.append((W / 2 + r * math.cos(t), ys + rry * math.sin(t)))
    pts.append((x0, ys))
    for i in range(9):                     # bottom-left corner
        t = math.pi + (math.pi / 2) * i / 8
        pts.append((x0 + rb + rb * math.cos(t), yb + rb + rb * math.sin(t)))
    return poly(pts)


def slab(cs, z0, z1):
    return cs.extrude(z1 - z0).translate((0, 0, z0))


def cyl(cx, cy, z0, z1, d):
    return (Manifold.cylinder(z1 - z0, d / 2, d / 2, SEG)
            .translate((cx, cy, z0)))


def union(parts):
    out = Manifold()
    for p in parts:
        out = out + p
    return out


# ---------------------------------------------------------------------------
# BODY
# ---------------------------------------------------------------------------
body = slab(outline2(), 0.0, FP_T)

# --- crescent ---------------------------------------------------------------
# The cavity wall stands proud of the back face; the acrylic pocket and the air
# gap are one bore through it, open at the back so the acrylic and then the LED
# carrier go in from behind.
#
# >>> THE WALL RUNS TO CARRIER_Z0, NOT CAV_Z. CAV_Z is where the LED emitting
# >>> face sits -- one DIFF_GAP behind the acrylic. The strip is LED_STRIP_T
# >>> thick BEHIND that, so a wall stopping at CAV_Z would leave the ribbon
# >>> standing proud in a 3 mm gap all the way round and give the carrier
# >>> nothing to land on. Running it the extra LED_STRIP_T shrouds the strip and
# >>> makes the wall's back face the carrier's seating plane.
# >>> AND ITS FLOOR IS DRAFTED. See BAFFLE_DROP in enclosure_geom: row 0's ribbon
# >>> hangs 2.4 mm below the baseline and used to sit 703 mm^3 inside this bar.
# >>> The floor keeps the baseline at the facade -- where the mic array is, 1.6 mm
# >>> behind it -- and slopes outward to BAFFLE_DROP by the time it reaches the
# >>> carrier, where nothing is underneath. The mic channel ends at z=5.0 and the
# >>> ramp starts at 4.7, so it sees 0.06 mm.
# >>>
# >>> BUILT AS TWO LOFTS AND A SUBTRACTION, NOT ONE HULL. The wall is a RING, and a
# >>> ring is not convex -- hulling it would fill the cavity solid. Outer and inner
# >>> are each convex (half-ellipse plus a rectangular skirt, tangent-continuous at
# >>> the springing line), so each lofts exactly, and the ring is their difference.
BAFFLE_RAMP_Z0 = DIFF_LIP + DIFF_REBATE      # start behind the acrylic


def _cav_outline(skirt):
    return half_disc(W / 2, CRES_Y, CAV_R, skirt=CAV_WALL + skirt, ry=CAV_RY)


def _bore_outline(skirt):
    return half_disc(W / 2, CRES_Y, DIFF_R, skirt=skirt, ry=DIFF_RY)


def _loft2(cs_a, za, cs_b, zb):
    P = [(float(x), float(y), float(za)) for x, y in cs_a.to_polygons()[0]]
    P += [(float(x), float(y), float(zb)) for x, y in cs_b.to_polygons()[0]]
    return Manifold.hull_points(P)


# >>> THE RAMP FINISHES AT CAV_Z, NOT AT THE CARRIER -- and getting that wrong
# >>> cost 0.6 mm of drop. The first version lofted to CARRIER_Z0 + 1.0, using the
# >>> "+1" purely as a cutting overrun; but the overrun is INSIDE the loft, so it
# >>> stretched the ramp over 15.13 mm instead of 12.0 and the floor was still
# >>> 0.02 mm above the ribbon where the strip begins. 703 mm^3 became 0.18 -- small
# >>> enough to look like a rounding artefact and not be.
# >>> CAV_Z is where the LED emitting face sits, so it is the SHALLOWEST z the
# >>> ribbon occupies and therefore the binding one. Ramp to full drop by then, and
# >>> hold it flat the rest of the way; the overrun is a separate straight piece.
BAFFLE_RAMP_Z1 = CAV_Z
_cav_outer = (slab(_cav_outline(0.0), 0.0, BAFFLE_RAMP_Z0)
              + _loft2(_cav_outline(0.0), BAFFLE_RAMP_Z0,
                       _cav_outline(BAFFLE_DROP), BAFFLE_RAMP_Z1)
              + slab(_cav_outline(BAFFLE_DROP), BAFFLE_RAMP_Z1, CARRIER_Z0))
_cav_inner = (slab(_bore_outline(0.0), -1.0, BAFFLE_RAMP_Z0)
              + _loft2(_bore_outline(0.0), BAFFLE_RAMP_Z0,
                       _bore_outline(BAFFLE_DROP), BAFFLE_RAMP_Z1)
              + slab(_bore_outline(BAFFLE_DROP), BAFFLE_RAMP_Z1,
                     CARRIER_Z0 + 1.0))
body = body + (_cav_outer - _cav_inner)

# (The LED carrier fixing pads used to be built HERE, and it was wrong -- see
#  the note where they are actually built, below the cuts.)

# --- wire exit for the LED crescent -----------------------------------------
# >>> THE LEFT FLANK, NOT THE BOTTOM BAR. The first version notched the bar that
# >>> closes the bottom of the cavity, which was the right MATERIAL and the wrong
# >>> face: the wires are meant to leave sideways out of the bottom-left corner,
# >>> not downward through the floor.
# >>>
# >>> AND THE TWO DIMENSIONS SWAP WHEN THE FACE DOES. On the bottom bar, "5 tall"
# >>> could only mean z, because the bar is 2 mm thick in y. On the LEFT FLANK the
# >>> face you are looking at is the y-z plane: height is y, and the horizontal
# >>> direction is DEPTH. So 10 wide is 10 in z and 5 tall is 5 in y. That is not a
# >>> re-reading for convenience -- it is forced independently by the lowest LED
# >>> carrier fixing pad, whose underside is only 4.43 mm above the cavity floor.
# >>> A 10 mm span in y would have destroyed that pad; 5 mm clears it.
# >>> THE BIG DIMENSION IS THE WIDTH UP THE FLANK, NOT THE DEPTH. It was built
# >>> 10 deep x 5 tall; the wire wants the opposite -- a wide, shallow slot. Depth
# >>> is now 6 and the width runs up the flank.
# >>>
# >>> AND ITS FLOOR FOLLOWS THE BAFFLE DRAFT. A flat-bottomed slot would have to
# >>> start at the floor's HIGHEST point across its depth, throwing away the 0.97 mm
# >>> the draft just bought at the back. Lofting the bottom between the floor
# >>> heights at the two ends gives the full opening AND makes "no floor removed"
# >>> true by construction rather than by a check -- the cut's underside IS the
# >>> floor, ruled between the same two points.
LED_WIRE_PAD_TRIM_MAX = 1.5   # how much of a fixing pad the exit may eat
PAD_PILOT_WALL_MIN = 1.2      # wall that must survive beside the pad's screw pilot
LED_WIRE_D = 6.0                        # DEPTH into the part (z)
LED_WIRE_H_WANT = 9.0                   # requested width, up the flank
# >>> IT STARTS AT THE CAVITY FLOOR, NOT BELOW IT. This was CRES_Y - CAV_WALL,
# >>> which reached down THROUGH the bar that closes the bottom of the cavity --
# >>> taking 5 mm off its left end. None of the bottom may go: the exit is purely a
# >>> side feature, and the floor stays continuous so the wire has something to lie
# >>> on as it runs out.
# >>> Starting at CRES_Y means the exit runs INTO the lowest carrier fixing pad,
# >>> whose underside is 4.43 mm up. That is accepted, not an oversight: the pad
# >>> gets trimmed 0.57 mm and keeps 1.63 mm of wall beside its pilot hole. The
# >>> check below bounds the trim rather than forbidding it.
LED_WIRE_Z0 = CARRIER_Z0 - LED_WIRE_D   # open at the carrier face


def baffle_floor(z):
    """y of the cavity floor at depth z -- the drafted baffle, one definition."""
    f = min(1.0, max(0.0, (z - BAFFLE_RAMP_Z0) / (BAFFLE_RAMP_Z1 - BAFFLE_RAMP_Z0)))
    return CRES_Y - BAFFLE_DROP * f


# >>> THE TOP IS SET BY THE PAD'S SCREW PILOT, so it is DERIVED, not requested. 9 mm
# >>> up the flank would put the cut 0.34 mm PAST the lowest fixing pad's pilot bore
# >>> -- through the hole, not near it. The pilot needs wall all round or the screw
# >>> splits it, so the requested width is capped by that and the real figure is
# >>> reported rather than the asked-for one.
_pad_lo0 = min(carrier_pads(),
               key=lambda p: ((W / 2 + p[0]) - (W / 2 - CAV_R)) ** 2
               + ((CRES_Y + p[1]) - CRES_Y) ** 2)
LED_WIRE_TOP = min(CRES_Y + LED_WIRE_H_WANT - BAFFLE_DROP,
                   (CRES_Y + _pad_lo0[1]) - PAD_PILOT_D / 2 - PAD_PILOT_WALL_MIN)
LED_WIRE_Y0 = baffle_floor(LED_WIRE_Z0)          # shallow end, the higher floor
LED_WIRE_Y0_DEEP = baffle_floor(CARRIER_Z0)      # deep end, the lower floor
LED_WIRE_H = LED_WIRE_TOP - LED_WIRE_Y0          # width at the shallow end
LED_WIRE_H_DEEP = LED_WIRE_TOP - LED_WIRE_Y0_DEEP
# The flank is ~2.0 mm thick and leans slightly with the ellipse, so cross it with
# margin rather than trying to hit a moving surface exactly.
LED_WIRE_X0 = W / 2 - CAV_R - 1.0
LED_WIRE_X1 = W / 2 - DIFF_R + 3.0

cuts = []
_wxw = LED_WIRE_X1 - LED_WIRE_X0
cuts.append(_loft2(rect2(LED_WIRE_X0, LED_WIRE_Y0, _wxw, LED_WIRE_H),
                   LED_WIRE_Z0,
                   rect2(LED_WIRE_X0, LED_WIRE_Y0_DEEP, _wxw, LED_WIRE_H_DEEP),
                   CARRIER_Z0 + 1.0))
cuts.append(slab(half_disc(W / 2, CRES_Y, DIFF_R, ry=DIFF_RY), DIFF_LIP, CAV_Z + 1))
cuts.append(slab(half_disc(W / 2, CRES_Y, CRES_R, ry=CRES_RY), -1.0, DIFF_LIP))

# --- clock: ONE open aperture, no per-pixel holes ---------------------------
# The matrices seat on the BACK FACE, not in a pocket. A pocket would locate the
# PAIR; the two boards are only loosely soldered to each other, so each one is
# located by its OWN posts instead and the pair is clamped by clips all round.
MTX_X0 = W / 2 - TRAY_W / 2                # left edge of the butted pair
# >>> ONE SQUARE WINDOW PER LED, cut only through the facade lip. Positions come
# >>> from mtx_led_xy(), which applies the same board->part flip as the mounting
# >>> holes -- the grid sits 3.683 from one board edge and 3.937 from the other,
# >>> so reading it unflipped would shift all 288 windows by 0.254 mm.
_w = MTX_WINDOW
for _lx, _ly in mtx_led_xy(MTX_X0, TRAY_Y0):
    cuts.append(slab(rect2(_lx - _w / 2, _ly - _w / 2, _w, _w), -1.0, MTX_INSET))
# ...and behind the facade lip, a pocket the board and its clips drop into.
# Sized to clear the clip beams AND leave a flex slot behind each, or the clips
# would be fused to the pocket wall along their whole length and could not move.
MTX_POCKET = CLIP_GAP + CLIP_T + MTX_CLIP_FLEX
_pocket = slab(rect2(MTX_X0 - MTX_POCKET, TRAY_Y0 - MTX_POCKET,
                     TRAY_W + 2 * MTX_POCKET, TRAY_H + 2 * MTX_POCKET),
               MTX_INSET, FP_T + 1.0)

# --- pin gutters along the two long edges -----------------------------------
# >>> DERIVED FROM THE LED FIELD, NOT FROM A VENDOR HEADER COORDINATE I DO NOT
# >>> HAVE. The matrix's fab print is not in hand, so rather than guess where the
# >>> header row sits, the gutter takes the WHOLE margin between the board edge and
# >>> the first LED window. Any 0.1"-pitch row in that margin is covered wherever
# >>> it actually is, and the number that matters (how much lip is left in front)
# >>> does not depend on the guess.
_led = mtx_led_xy(MTX_X0, TRAY_Y0)
_ly_min, _ly_max = min(y for _, y in _led), max(y for _, y in _led)
_gut_lo = _ly_min - MTX_WINDOW / 2 - MTX_GUTTER_WEB      # inner edge, bottom
_gut_hi = _ly_max + MTX_WINDOW / 2 + MTX_GUTTER_WEB      # inner edge, top
MTX_GUTTERS = [(TRAY_Y0, _gut_lo), (_gut_hi, TRAY_Y0 + TRAY_H)]
_gz0 = MTX_INSET - MTX_GUTTER_D
# >>> UNIONED WITH THE POCKET BEFORE SUBTRACTING, not cut separately. Cut on its
# >>> own the gutter's back face would land exactly on the pocket floor at
# >>> z = MTX_INSET -- a coplanar pair, which is how this part has produced
# >>> zero-area facets and phantom extra bodies twice before. Unioned first, that
# >>> internal plane never exists.
_gut = _pocket
for _y0, _y1 in MTX_GUTTERS:
    _gut = _gut + slab(rect2(MTX_X0, _y0, TRAY_W, _y1 - _y0), _gz0, FP_T + 1.0)
# ...then give each post its pedestal back, in the lip band only. Above
# MTX_INSET the collar must not exist or it would stand proud in the pocket and
# hold the board off by exactly what the gutter was meant to recover.
_collars = []
for _b in range(MTX_N):
    for _hx, _hy in MTX_HOLES:
        _collars.append(cyl(MTX_X0 + _b * MTX_BOARD_W + _hx, TRAY_Y0 + _hy,
                            _gz0 - 0.6, MTX_INSET,
                            MTX_POST_D + 2 * MTX_POST_COLLAR))
_gut = _gut - union(_collars)
cuts.append(_gut)
MTX_Z0 = MTX_INSET                         # matrix front face, ON the lip
MTX_ZB = MTX_Z0 + MTX_PCB_T                # matrix back face
BP_Z0  = MTX_ZB + MTX_STACK_GAP            # backpack front
BP_ZB  = BP_Z0 + MTX_BP_T                  # backpack back -- CLIPS HOOK HERE

# --- speakers ---------------------------------------------------------------
for sx in (SPK_X, W - SPK_X):
    cuts.append(cyl(sx, SPK_Y, -1.0, FP_T + 1, SPK_GRILLE))

# --- mic array --------------------------------------------------------------
mic_ch_w = MIC_PCB_W + 2 * MIC_FIT
mic_ch_h = MIC_PCB_H + 2 * MIC_FIT
MIC_Z0 = FP_T - MIC_CHAN_D
cuts.append(slab(rect2(W / 2 - mic_ch_w / 2, MIC_Y0 - MIC_FIT,
                       mic_ch_w, mic_ch_h), MIC_Z0, FP_T + 1))

body = body - union(cuts)

# ---------------------------------------------------------------------------
# ADDITIVE FEATURES (all behind the facade, all growing upward off the bed)
# ---------------------------------------------------------------------------
adds = []

# --- LED carrier fixing pads ------------------------------------------------
# Local thickenings on the INSIDE of the cavity wall, at the angles
# enclosure_geom.pad_angle_bands() found clear of the pixels, the end stops and
# the ribbons. They run the full height of the wall, so they also buttress what
# is otherwise a 2 mm x 19 mm unsupported fin -- that wall's aspect ratio is set
# by optics, not structure, and it prints better braced.
#
# >>> THESE MUST BE BUILT AFTER THE CUTS, AND THEY ONCE WERE NOT. Added up with
# >>> the cavity wall, they were promptly sliced away by the acrylic-pocket /
# >>> air-gap bore, which is a half_disc of DIFF_R running z=DIFF_LIP..CAV_Z+1 --
# >>> and the pads live INSIDE DIFF_R by definition, that being the entire point
# >>> of them. All that survived was 1.13 mm of stub at the very top, with an
# >>> 8 mm pilot drilling into thin air below it. The presence probe passed
# >>> because it happened to sample inside that stub.
#
# >>> THEY TAPER: wider at the base, PAD_W at the seating plane. Two reasons.
# >>> FDM prints face down here, so anything that gets WIDER as it rises
# >>> overhangs -- narrowing upward is the self-supporting direction and needs no
# >>> support inside an optical cavity, where support scarring would be visible
# >>> through the diffuser. And the flare is a gusset: it puts the material at
# >>> the root, where a boss standing 19 mm off a 2 mm wall wants to snap.
# >>> Everything the pad has to stay clear of -- ribbons, stops, pixels -- sits
# >>> at the TOP of the cavity, where the pad is at its narrowest PAD_W. The
# >>> flare only ever grows into the air gap, which is empty.
# How far past the cavity's inner face the ramp's apex is buried, so the tip
# starts inside solid wall rather than on its surface. A tip exactly ON the face
# is still a knife edge for the slicer to resolve.
APEX_BURY = 1.0


def _pad_axis(x, y):
    """Outward unit normal of the cavity ellipse at this pad's position -- the
    direction 'towards the wall'."""
    dx, dy = x - W / 2, y - CRES_Y
    nx, ny = dx / (DIFF_R_G ** 2), dy / (DIFF_RY_G ** 2)
    nl = math.hypot(nx, ny) or 1.0
    return nx / nl, ny / nl


def carrier_pad_solid(x, y, grow=0.0):
    """One fixing pad: a 45 deg cone growing out of the wall from the acrylic
    pocket floor, then a drafted column up to the seating plane.

    Built by a named function because the diffusion-air-gap clash has to subtract
    the EXACT same solid. An approximation there (it used to be a plain cylinder
    of PAD_W) stops matching the moment the pad grows a taper, and the check then
    reports interference that is really just its own bad stand-in."""
    r1 = PAD_W / 2 + grow

    # >>> THE RAMP IS A SKEWED CONE WITH ITS APEX IN THE WALL, NOT A STRAIGHT ONE
    # >>> ON THE PAD AXIS. A straight cone tapering to a point on the pad's own
    # >>> centreline puts that point PAD_OFFSET_IN (1.55 mm) clear of the wall,
    # >>> hanging in the middle of the cavity with nothing beneath it -- the bore
    # >>> has removed everything below PAD_Z0. On FDM that first layer prints into
    # >>> thin air. It is the classic floating tip: it looks like a tidy taper in
    # >>> section and is unbuildable.
    # >>>
    # >>> Instead the apex is pushed OUTWARD, past the cavity's inner face and
    # >>> into the wall's own material, and the solid is the convex hull of that
    # >>> apex and the shaft's base circle. Every layer of the result therefore
    # >>> touches the wall -- the pad grows gradually out of it rather than
    # >>> appearing beside it -- and the whole thing is one half-cone leaning on
    # >>> a face that is already solid all the way down.
    _o = _pad_axis(x, y)                       # outward normal at this pad
    apex = (x + _o[0] * (PAD_OFFSET_IN + APEX_BURY),
            y + _o[1] * (PAD_OFFSET_IN + APEX_BURY))
    ramp = Manifold.batch_hull([
        Manifold.cylinder(0.01, 0.35, 0.35, SEG)
        .translate((apex[0], apex[1], PAD_Z0 - grow)),
        Manifold.cylinder(0.01, r1, r1, SEG)
        .translate((x, y, PAD_Z0 + PAD_RAMP)),
    ])
    shaft = (Manifold.cylinder(CARRIER_Z0 - PAD_Z0 - PAD_RAMP + 2*grow, r1, r1,
                               SEG)
             .translate((x, y, PAD_Z0 + PAD_RAMP)))
    pad = ramp + shaft
    # >>> CLIPPED TO THE CAVITY'S OUTER FACE. A round boss centred inside the
    # >>> wall grows BOTH ways, and the base flare -- the whole point of which is
    # >>> to put material at the root -- pushed 1.2 mm straight out through the
    # >>> wall's outer face and into the 0.9 mm rim, which is the dome's
    # >>> retaining-rib band. That is the one place on this part where a boss
    # >>> jams the whole assembly.
    # >>> `pad_wall_margins()` did not catch it because it measured the SHAFT
    # >>> radius and the flare is bigger. Rather than fix only the number, the
    # >>> geometry is now clipped: intersecting with the cavity envelope means no
    # >>> pad can EVER break the outer plane, whatever draft it is given. The
    # >>> outer side of the boss simply comes out flush with the wall.
    return pad ^ slab(half_disc(W / 2, CRES_Y, CAV_R + grow,
                                skirt=CAV_WALL, ry=CAV_RY + grow),
                      -1.0, CARRIER_Z0 + 1.0)


pad_pts, pad_solids = [], []
for _px, _py, _deg in carrier_pads():
    _x, _y = W / 2 + _px, CRES_Y + _py
    pad_pts.append((_x, _y))
    pad_solids.append(carrier_pad_solid(_x, _y))
adds.extend(pad_solids)

# --- matrix locating posts + seating pads, ONE SET PER BOARD ----------------
# Per board: two posts through its diagonal O2.0 holes, and two plain pads on
# the other diagonal so it seats on four points and cannot rock.
mtx_posts, mtx_pads = [], []
for b in range(MTX_N):
    bx = MTX_X0 + b * MTX_BOARD_W
    for hx, hy in MTX_HOLES:
        px, py = bx + hx, TRAY_Y0 + hy
        mtx_posts.append((px, py))
        # rooted on the facade LIP now, not on the plate's back face
        adds.append(cyl(px, py, MTX_Z0, MTX_Z0 + MTX_PCB_T + 0.1, MTX_POST_D))
        adds.append(Manifold.cylinder(MTX_POST_TIP, MTX_POST_D / 2,
                                      MTX_POST_D * 0.2, SEG)
                    .translate((px, py, MTX_Z0 + MTX_PCB_T + 0.1)))
    # >>> NO SEATING PADS ANY MORE. They existed to stand the board off the flat
    # >>> back face onto four defined points; the board now seats on the back of
    # >>> the facade lip, which is a defined surface by construction. Pads on top
    # >>> of it would only lift the board back off the datum they were meant to
    # >>> establish. Their positions are still recorded so the drawings and the
    # >>> interference check know where the board is supported.
    for hy in (MTX_PAD_EDGE, MTX_BOARD_H - MTX_PAD_EDGE):
        mtx_pads.append((bx + MTX_BOARD_W / 2, TRAY_Y0 + hy))

# --- gasket lands, then the ports straight through them ---------------------
for mxc in mic_x():
    adds.append(cyl(mxc, MIC_Y, MIC_Z0, MIC_Z0 + MIC_LAND_H,
                    MIC_PORT_D + 2 * MIC_GASKET))
# --- mic board fixing bosses ------------------------------------------------
# >>> THE BOSS USED TO STAND 2.5 mm ABOVE THE BOARD'S TOP FACE, so a screw head
# >>> bottomed out on the boss and never touched the PCB. The array was not being
# >>> held down at all -- it just had a post through its hole. That is why the
# >>> foam could not be relied on to seal: nothing was compressing it.
# >>> The boss now stops MIC_SCREW_SINK below the board's top face, so the head
# >>> lands on the PCB and pulls it onto the gasket lands. Short on purpose: the
# >>> array only has to be held against thin foam, not clamped.
MIC_PCB_T     = 1.6                       # array board thickness
# >>> FLUSH WITH THE SEATING PLANE, NOT PROUD OF IT. Sinking the boss to just
# >>> under the board's TOP face was still wrong, because the boss is Ø5.0 and the
# >>> board's hole is M3 -- Ø3.2. The board cannot pass over it at all, so it was
# >>> resting on the boss top and sitting 1.2 mm high, which is exactly why the
# >>> foam was never getting compressed.
# >>> The boss is now a flat pad level with the gasket lands: the board lands on
# >>> the lands, the screw passes through its hole and threads into the pilot bored
# >>> down into the facade. Nothing protrudes into the board's space.
MIC_BOSS_TOP  = MIC_Z0 + MIC_LAND_H
for sgn in (-1, 1):
    adds.append(cyl(W / 2 + sgn * MIC_BOSS_X, MIC_Y, MIC_Z0,
                    MIC_BOSS_TOP, MIC_BOSS_D))

# --- speaker nub posts (TOP AND BOTTOM) -------------------------------------
# >>> THE SPEAKERS ARE ROTATED 90 DEG, so the nubs are TOP AND BOTTOM and the
# >>> posts go WITH THEM. This block used to build the posts on the FLANKS, at
# >>> px = sx +/- (SPK_BODY_W/2 + SPK_FIT + pw/2) -- x = 5.25 / 56.95 and their
# >>> mirrors. That is a leftover from the pre-rotation speaker model and it was
# >>> the single root cause of six separate failures: the outboard pair stood in
# >>> the dome's groove band and the inboard pair stood inside the matrix
# >>> footprint. If a probe ever finds a wall at x ~ 5 or ~ 57 again, look here
# >>> first.
#
# NO RIBS, on any face. Two screws on the body's vertical centreline fix x, y
# and rotation between them, so nothing else is needed -- and there is nowhere
# to put a rib anyway: the width chain budgets SPK_FLANK = 1.0 per flank as pure
# clearance, and a 1 mm fin there would land in the dome's retaining-rib band.
#
# The nub lands SPK_NUB_Z behind the speaker's front face, and that face sits on
# the back of the facade -- so the post top is at FP_T + SPK_NUB_Z and the screw
# goes in FROM BEHIND, through the nub, into the post.
#
# >>> POST WIDTH IS SET BY THE NUB, NOT BY THE BODY. A post scaled off the body
# >>> (0.60 x SPK_BODY_W = 27) reaches x = 44.6, which is 1.4 mm from the mic
# >>> PCB now that the array has come down. SPK_POST_W is nub + wall = 10, which
# >>> keeps it ~10 mm clear -- see CLR_POST_MIC in the clearance table.
for sx in (SPK_X, W - SPK_X):
    for ybase in (SPK_Y0 - SPK_FIT - SPK_POST_H_Y, SPK_Y1 + SPK_FIT):
        adds.append(slab(rect2(sx - SPK_POST_W / 2, ybase,
                               SPK_POST_W, SPK_POST_H_Y),
                         FP_T, FP_T + SPK_NUB_Z))

# --- stiffening -------------------------------------------------------------
# A 4 mm plate this size with two sealed boxes bolted to it will drum. There is
# very little free facade to rib, though: below the tray there is 1 mm to the
# module edge, above it 1.4 mm to the mic channel, and outboard of the speakers
# about 1 mm to the flank. Two places genuinely have room:
#
#  1. A full-width SPINE in the band between the speaker tops and the cavity
#     wall. This is the widest unsupported span on the part, and the spine ties
#     both speaker seats into the cavity wall -- which is itself a 12.7 mm tall
#     stiffener running the whole upper half.
#     It stops BOSS_EDGE short of the outline at each end -- it is a boss on the
#     back face, so it has to clear the dome's retaining rib like everything
#     else. An earlier version ran it edge to edge and jammed the joint.
# It sits BETWEEN the matrix top and the speaker tops, spanning the middle only
# -- the mic channel now occupies the band that used to be free above the
# speakers, and the speakers themselves own the outer thirds.
SPINE_Y0 = TRAY_Y1 + CLIP_GAP + CLIP_T + 1.0
SPINE_Y1 = SPK_Y1 - 1.0
SPINE_X0 = SPK_X + SPK_BODY_W/2 + SPK_FIT + 1.0
# a rib CENTRED in the band, not a pad filling it
_sy = (SPINE_Y0 + SPINE_Y1) / 2 - RIB_T / 2
adds.append(slab(rect2(SPINE_X0, _sy, W - 2*SPINE_X0, RIB_T),
                 FP_T, FP_T + RIB_H))
#  2. A SECOND SPINE in the matching band BELOW the matrix.
#
# >>> THIS REPLACES THE OLD "SHORT RIBS INBOARD FROM EACH SPEAKER". Those ran at
# >>> y = SPK_Y +/- RIB_T/2, reaching 11 mm in from each speaker towards the
# >>> clock. That was safe when the matrix sat hard down on the floor. It is not
# >>> any more: the clock is now CENTRED ON THE SPEAKERS (see TRAY_Y0), so
# >>> SPK_Y *is* the matrix mid-height, and each rib ran straight through the
# >>> boards -- 49.8 mm^3 into the matrix envelope, into 288 LEDs, and through
# >>> the end clips' hook zone. Four separate failures, one rib.
# >>>
# >>> There is nowhere to put them any more: from the speaker seat to the end
# >>> clip's outer face is 0.77 mm. So the stiffening moves to the band BELOW
# >>> the matrix, which is the mirror of the spine above it and is genuinely
# >>> empty -- and a symmetric pair of spines braces the plate better than one
# >>> spine plus two stubs did.
SPINE2_Y0 = BP_T + BOSS_EDGE                       # clear the back-face keep-out
SPINE2_Y1 = TRAY_Y0 - CLIP_GAP - CLIP_T - 1.0      # clear the bottom clips
# >>> THE LOWER BAND IS WIDE ENOUGH FOR TWO. It spans 10.9 mm against the upper
# >>> band's 6.6, and two ribs brace a panel better than one twice as thick --
# >>> they break the unsupported span into three instead of two.
# >>> SPACED TO THE BAND'S EDGES, NOT AT THIRDS. Placing two ribs at 1/3 and 2/3
# >>> of a 10.9 mm band leaves 0.65 mm between them -- narrower than a nozzle, so
# >>> it prints as one blob with a defect down the middle and stiffens like a
# >>> single fat rib. Pushed to the edges the gap is 4.9 mm, they brace two
# >>> separate lines of the panel, and each one is a clean 3 mm wall.
RIB_MIN_GAP = 2.0
_n2 = 2 if (SPINE2_Y1 - SPINE2_Y0) >= 2 * RIB_T + RIB_MIN_GAP else 1
_rib2_y = ([SPINE2_Y0, SPINE2_Y1 - RIB_T] if _n2 == 2
           else [(SPINE2_Y0 + SPINE2_Y1) / 2 - RIB_T / 2])
for _sy2 in _rib2_y:
    adds.append(slab(rect2(SPINE_X0, _sy2, W - 2*SPINE_X0, RIB_T),
                     FP_T, FP_T + RIB_H))

body = body + union(adds)

# ---------------------------------------------------------------------------
# TRAY CLIPS -- cantilevers on the tray's two END faces
# ---------------------------------------------------------------------------
# Why the ends: below the tray there is 1 mm to the module's bottom edge and
# above it 2 mm to the mic channel, so the long sides have nowhere to root a
# clip. The ends have 13.9 mm of clear facade before the speaker seats.
# Why the corners: the tray's end walls have an 18 mm wire notch dead centre.
def clip(axis, face, sgn, centre, hook_z):
    """One cantilever, on any of the four sides.

    `axis` is the direction the clip FACES: 'x' for the two ends, 'y' for the
    top and bottom edges. `sgn` is +1 when the clip sits on the high side of
    `face`, so its hook reaches back in the negative direction.

    The profile is drawn in (u, z) -- the part's own cross-section -- then swung
    up so the drawn z becomes real z. Every overhang is therefore a 45 deg facet
    in the print's vertical plane:
        root ---- beam ---- 45 deg retain facet ---- shallow lead-in ramp
    """
    ui = face + sgn * CLIP_GAP                      # inner face of the beam
    uo = ui + sgn * CLIP_T                          # outer face
    hook = ui - sgn * CLIP_REACH                    # hook tip, over the board
    z_top = hook_z + CLIP_RUN + CLIP_RAMP + CLIP_TAIL
    pts = [
        (ui, CLIP_ROOT_Z),                          # root, on the pocket floor
        (ui, hook_z),                               # up the inner face
        (hook, hook_z + CLIP_RUN),                  # 45 deg retain facet
        (ui, hook_z + CLIP_RUN + CLIP_RAMP),        # lead-in ramp
        (ui, z_top),
        (uo, z_top),                                # over the top, back down
        (uo, CLIP_ROOT_Z),
    ]
    # extrude gives width along local z; rotate x+90 stands the profile up and
    # lays the width along y, giving x=u.
    s = poly(pts).extrude(CLIP_W).rotate((90, 0, 0)).translate((0, CLIP_W, 0))
    if axis == "x":                                 # u is x, width along y
        return s.translate((0, centre - CLIP_W / 2, 0))
    # u is y: swap the axes (rotate about z), then centre the width in x
    return (s.rotate((0, 0, 90)).translate((CLIP_W, 0, 0))
             .translate((centre - CLIP_W / 2, 0, 0)))


mtx_x0, mtx_x1 = MTX_X0, MTX_X0 + TRAY_W
mtx_y0, mtx_y1 = TRAY_Y0, TRAY_Y0 + TRAY_H
# Two clips on each long edge and one on each end -- six, on all four sides.
# The long-edge clips sit over the SEAM and the outer thirds, so each board is
# clamped near its own centre rather than relying on the solder joint.
CLIP_TOP_X = [W / 2 - TRAY_W / 4, W / 2 + TRAY_W / 4]
CLIP_BOT_X = [W / 2 - TRAY_W / 4, W / 2 + TRAY_W / 4]
# >>> NO CLIPS ON THE ENDS -- THE STEMMA QT PORTS LIVE THERE. Adafruit's driver
# >>> carries a JST-SH connector on each SHORT edge, and gen_tray.py already knew
# >>> it: that part notches both END walls 18 mm tall and centred, and puts its
# >>> four snap fingers on the LONG walls only. This file grew end clips anyway,
# >>> centred on exactly the band the notch exists to keep clear -- they would
# >>> have landed on the connectors, and there is no way to dodge: an 18 mm port
# >>> band in a 27.94 mm board leaves 4.97 mm at each end, and a clip is 6.
# >>> Four clips on the long edges is what the tray proved, at the same 25/75 %
# >>> spacing. The ends stay free for the cables.
_CLIP_AXES = ["y"] * (len(CLIP_BOT_X) + len(CLIP_TOP_X))
MTX_PORT_BAND = 18.0        # from gen_tray.py: clears TWO stacked STEMMA QT ports
clips = [clip("y", mtx_y0, -1, cx, BP_ZB + CLIP_STACK_CLR) for cx in CLIP_BOT_X]
clips += [clip("y", mtx_y1, +1, cx, BP_ZB + CLIP_STACK_CLR) for cx in CLIP_TOP_X]
body = body + union(clips)

# ---------------------------------------------------------------------------
# CONTAINMENT GUARD
# ---------------------------------------------------------------------------
# Nothing may escape the module outline -- it has to slide up a groove in the
# dome, so a boss hanging 1 mm past the edge jams the whole assembly. Trimming
# against the outline prism makes that structurally impossible rather than
# something to remember. (An earlier revision had ribs 10 mm off the edge.)
before = body.bounding_box()
body = body ^ slab(outline2(), -1.0, CAV_Z + 20.0)
after = body.bounding_box()
trimmed = (abs(before[0] - after[0]) + abs(before[3] - after[3])
           + abs(before[1] - after[1]) + abs(before[4] - after[4]))

# ---------------------------------------------------------------------------
# PILOT HOLES -- cut last, so nothing fills them back in
# ---------------------------------------------------------------------------
pilots = []
for sx in (SPK_X, W - SPK_X):
    for py in (SPK_Y0 - SPK_FIT - (SPK_NUB_PROJ + SPK_POST_WALL)/2,
               SPK_Y1 + SPK_FIT + (SPK_NUB_PROJ + SPK_POST_WALL)/2):
        pilots.append(cyl(sx, py,
                          FP_T + SPK_NUB_Z - SPK_PILOT_Z, FP_T + SPK_NUB_Z + 1,
                          SPK_PILOT_D))
# >>> THE PILOT NOW GOES DOWN INTO THE FACADE, not up through a boss that is no
# >>> longer there. The boss is only MIC_BOSS_TOP - MIC_Z0 tall now, so on its own
# >>> it gives a thin screw almost nothing to bite. Running the pilot into the
# >>> 1.6 mm of facade under the channel roughly doubles the thread engagement,
# >>> and it stays BLIND -- MIC_PILOT_FLOOR of skin is left so it cannot show
# >>> through the front face.
# >>> Thread depth is now the facade under the channel, minus the skin: about
# >>> 1.5 mm for an M2. That is under one diameter of engagement -- fine for
# >>> holding a light board against thin foam, and it is the price of having the
# >>> board sit right down on the tape. If it ever strips, the fix is a longer
# >>> screw into a boss on the BACK of the plate, not a taller one in front.
MIC_PILOT_FLOOR = 0.4                     # skin left in front of the pilot
for sgn in (-1, 1):
    pilots.append(cyl(W / 2 + sgn * MIC_BOSS_X, MIC_Y,
                      MIC_PILOT_FLOOR, MIC_BOSS_TOP + 0.3, MIC_PILOT_D))
for mxc in mic_x():
    pilots.append(cyl(mxc, MIC_Y, -1.0, MIC_Z0 + MIC_LAND_H + 1, MIC_PORT_D))
# LED carrier pilots. Blind, from the BACK -- they must not break through into
# the diffusion cavity or the acrylic pocket, so they stop PAD_PILOT_Z short of
# CARRIER_Z0 and never reach DIFF_LIP+DIFF_REBATE. Checked below.
for _px, _py, _ in carrier_pads():
    pilots.append(cyl(W / 2 + _px, CRES_Y + _py,
                      CARRIER_Z0 - PAD_PILOT_Z, CARRIER_Z0 + 1, PAD_PILOT_D))
body = body - union(pilots)

# ---------------------------------------------------------------------------
# SPLIT FOR THE PRINT BED
# ---------------------------------------------------------------------------
# The module is 250.8 wide and the target bed is 220. No rotation helps -- this
# is a D, so rotating only grows the bounding box, and the 45 deg tilt that does
# fit geometrically would stand the facade up at 45 deg on supports, which ruins
# the one surface anyone looks at. So it splits.
#
# WHERE: a single seam, threading the only usable corridor across the width --
# between the left speaker seat (ends x=70.3) and the matrix's end clip (starts
# x=83.4). That keeps the ENTIRE clock on one piece, which matters: the two
# matrices are the thing that is not rigid, and putting a glue joint between
# them would undo the whole posts-and-clips arrangement. A centre seam would fit
# the bed just as well and is exactly the wrong place.
#
# HOW: a Z-LAP, not a butt joint. The front half of the plate carries on past
# the seam as a tongue; the back half of the other piece laps over it. Bosses
# are unaffected -- they all live above the lap plane, so each one lands whole
# on the right-hand piece rather than being cut in two.
# >>> THE LAP ZONE MUST CONTAIN NO BOSS THAT STANDS ON THINNED FACADE. The lap
# >>> plane sits at mid-thickness, and the mic channel's floor is exactly that
# >>> thick -- so a boss standing in the channel ends up ABOVE the plane (right
# >>> piece) while the floor it stands on is BELOW it (left piece), and the boss
# >>> prints as a floating island. That is what the per-half body count catches.
# >>> The usable corridor is therefore speaker seat (ends 70.3) -> first gasket
# >>> land (starts 77.25), 6.95 wide, and the lap has to live inside it.
# (SPLIT_X / LAP_* / PEG_* / BED are up top with the other print parameters --
#  the rib layout has to know where the seam is, and that happens earlier.)
BIG = 1000.0


def _halfspace(x0, x1, z0, z1):
    return slab(rect2(x0, -BIG / 2, x1 - x0, BIG), z0, z1)


if NEEDS_SPLIT:
    # left keeps everything before the lap, plus the front-layer tongue
    left_region = (_halfspace(-BIG, _L0, -BIG, BIG)
                   + _halfspace(_L0, _L1 - LAP_CLR, -BIG, LAP_Z - LAP_CLR))
    # right keeps everything after the lap, plus the back layer through it
    right_region = (_halfspace(_L1, BIG, -BIG, BIG)
                    + _halfspace(_L0 + LAP_CLR, _L1, LAP_Z, BIG))
    pegs, peg_holes = [], []
    for _py in PEG_Y:
        pegs.append(cyl(SPLIT_X, _py, LAP_Z - LAP_CLR,
                        LAP_Z - LAP_CLR + PEG_H, PEG_D))
        peg_holes.append(cyl(SPLIT_X, _py, LAP_Z - 0.3,
                             LAP_Z + PEG_H + 0.3, PEG_D + 2 * LAP_CLR))
    left_part = (body ^ left_region) + union(pegs)
    right_part = (body ^ right_region) - union(peg_holes)
    left_part = left_part ^ (body + union(pegs))
else:
    left_part = right_part = None

# ---------------------------------------------------------------------------
# EXPORT
# ---------------------------------------------------------------------------
# >>> WRITE TO MODEL_DIR. This file kept its own `base` pointing at the script
# >>> directory, so when solids moved into models/ every other generator followed
# >>> and this one did not. It carried on exporting to 3d-print/front-module.stl
# >>> while models/front-module.stl sat there STALE -- the run said "wrote 19046
# >>> triangles", the file in models/ had 19032, and every downstream measurement
# >>> was of a part three hours out of date.
base = MODEL_DIR


def write_stl(solid, name):
    m = solid.to_mesh()
    vv, ff = m.vert_properties[:, :3], m.tri_verts
    buf = bytearray(b"\0" * 80 + struct.pack("<I", len(ff)))
    for f in ff:
        a, b, c = vv[f[0]], vv[f[1]], vv[f[2]]
        ux, uy, uz = b - a
        vx, vy, vz = c - a
        nx, ny, nz = uy*vz - uz*vy, uz*vx - ux*vz, ux*vy - uy*vx
        L = math.sqrt(nx*nx + ny*ny + nz*nz) or 1.0
        buf += struct.pack("<12fH", nx/L, ny/L, nz/L, *a, *b, *c, 0)
    open(os.path.join(base, name), "wb").write(buf)
    return vv, ff


# >>> THE EXPORTED STL IS NOT IN DRAWING COORDINATES, AND THAT WILL CATCH YOU.
# >>> Everything above -- every dimension, every check, every drawing -- is in the
# >>> assembly's frame, where the module's outline sits at inset REVEAL and the
# >>> bottom plate occupies y < BP_T. The STL is shifted so the part's own corner
# >>> is the origin, which is what a slicer wants. The two frames differ by
# >>> (REVEAL, BP_T) = (3.6, 4.0).
# >>> Probing models/front-module.stl with assembly coordinates therefore reports
# >>> features missing that are perfectly present: a scan for the matrix clips
# >>> came back empty at every height above the beam, and the "obvious" reading
# >>> was that the clips had failed to build. They had not; the scan was 3.6 mm
# >>> and 4.0 mm out. `part_body` below exists precisely so the checks can work in
# >>> the assembly frame -- use THAT, or add the shift.
body = body.translate((-REVEAL, -BP_T, 0.0))        # part origin at its corner
V, F = write_stl(body, "front-module.stl")
if NEEDS_SPLIT:
    left_part = left_part.translate((-REVEAL, -BP_T, 0.0))
    right_part = right_part.translate((-REVEAL, -BP_T, 0.0))
    write_stl(left_part, "front-module-L.stl")
    write_stl(right_part, "front-module-R.stl")
    for _stale in ():
        pass
else:
    for _stale in ("front-module-L.stl", "front-module-R.stl"):
        _fp = os.path.join(base, _stale)
        if os.path.exists(_fp):
            os.remove(_fp)
bb = body.bounding_box()
say(f"wrote front-module.stl   {len(F)} triangles")
say(f"bbox        {bb[3]-bb[0]:.2f} x {bb[4]-bb[1]:.2f} x {bb[5]-bb[2]:.2f} mm")
say(f"STL frame   shifted ({-REVEAL:+.1f}, {-BP_T:+.1f}, +0.0) from assembly "
    f"coords -- probe the STL with that offset, or use part_body")
say(f"z stack     facade 0-{FP_T}   acrylic {DIFF_LIP}-{DIFF_LIP+DIFF_REBATE}"
    f"   air gap {DIFF_LIP+DIFF_REBATE}-{CAV_Z}   cavity wall to {CAV_Z}")
say(f"crescent    aperture R{CRES_R}  acrylic pocket R{DIFF_R}  "
    f"cavity wall R{DIFF_R}-{CAV_R}   LED field R{LED_R} (fade band "
    f"{CRES_R-LED_R:.0f})")
say(f"clock       {MTX_N*MTX_LED_COLS*MTX_LED_ROWS} square windows "
    f"{MTX_WINDOW} x {MTX_WINDOW} on a "
    f"{MTX_LED_PITCH} pitch, web {MTX_LED_PITCH-MTX_WINDOW:.2f}, "
    f"through a {MTX_INSET} mm lip")
say(f"            {MTX_N} matrices {MTX_BOARD_W} x {TRAY_H} butted = "
    f"{TRAY_W:.2f} wide, RECESSED -- front face {MTX_INSET} mm behind the "
    f"facade, seating on the aperture lip")
say(f"            LOOSELY SOLDERED PAIR -> {len(mtx_posts)} locating posts "
    f"({chr(216)}{MTX_POST_D} into their own {chr(216)}{MTX_HOLE_D} holes) + "
    f"seating on the lip (pads retired)")
say(f"            {len(clips)} clips on the LONG edges only (ends left free for "
    f"the STEMMA QT ports), {CLIP_W} wide, hook "
    f"{CLIP_ENGAGE} onto the STACK back at z={BP_ZB:.2f}, rooted at "
    f"{CLIP_ROOT_Z}, "
    f"{CLIP_T} thk, strain "
    f"{1.5*CLIP_T*CLIP_ENGAGE/(BP_ZB+CLIP_STACK_CLR-CLIP_ROOT_Z+CLIP_RUN)**2*100:.2f}%"
    f" ({CLIP_MAT})")
say(f"            stack: matrix {MTX_Z0}-{MTX_ZB} | gap | backpack "
    f"{BP_Z0}-{BP_ZB}")
say(f"speakers    grille {chr(216)}{SPK_GRILLE} thru; NO ribs (rotated mount); "
    f"posts {SPK_NUB_Z} tall with {chr(216)}{SPK_PILOT_D} x {SPK_PILOT_Z} pilots")
say(f"mic         channel {mic_ch_w:.1f} x {mic_ch_h:.1f} x {MIC_CHAN_D} deep; "
    f"4x {chr(216)}{MIC_PORT_D} ports on {chr(216)}{MIC_PORT_D+2*MIC_GASKET} "
    f"gasket lands")

# ---------------------------------------------------------------------------
# ENVELOPE INTERFERENCE TESTS
# ---------------------------------------------------------------------------
# Eyeballing a render does not prove a part fits. For every component this
# module carries, intersect its swept envelope with the printed solid: the
# result must be EXACTLY zero. Anything else is material where a component has
# to go, which is the one class of error that only shows up after a 9-hour
# print.
say("")
say("envelope interference (mm^3 of plastic inside a component's space)")
part_body = body.translate((REVEAL, BP_T, 0.0))     # back to drawing coords
bad = []


def clash(name, env, allow=0.0):
    v = (part_body ^ env).volume()
    ok = v <= allow + 1e-6
    say(f"  {'FAIL' if not ok else 'ok  '} {v:9.2f}   {name}")
    if not ok:
        bad.append((name, -1))
    return v


# The matrix pair. Everything from its front face to its back face must be free
# EXCEPT the locating posts, which are supposed to be inside its holes -- so the
# envelope has those holes punched out of it. The clip hooks deliberately
# overhang, but only ABOVE the back face.
mtx_env = rect2(mtx_x0, mtx_y0, TRAY_W, TRAY_H)
for _p in mtx_posts:
    mtx_env = mtx_env - disc2(_p[0], _p[1], MTX_HOLE_D / 2)
clash("matrix pair envelope (front -> back face, holes excepted)",
      slab(mtx_env, MTX_Z0, MTX_ZB))
clash("driver backpacks behind them",
      slab(rect2(mtx_x0, mtx_y0, TRAY_W, TRAY_H), BP_Z0, BP_ZB))
# The LEDs stand proud of the board front, so nothing may touch them: not the
# facade (they have to be inside the aperture) and not the seating pads or
# posts. Checked against ACTUAL LED positions -- a bounding box round the field
# clips the board corners, where the pads legitimately live.
# >>> ONE DEFINITION OF WHERE THE LEDs ARE. This block used to re-derive them
# >>> from its own copy of the pitch and origin -- and it did NOT apply the
# >>> board->part flip, so it disagreed with the windows by 0.254 mm. With only
# >>> 0.2 mm of clearance per side that is most of the margin, and the check duly
# >>> reported 42.61 mm^3 of interference that was entirely its own doing.
# >>> Third time this project has been bitten by a duplicated geometry
# >>> definition. It now calls the shared function, like the windows do.
LED_BODY = 1.6        # (?) 0603 package, long axis -- MEASURE if the fit is tight
led_xy = mtx_led_xy(MTX_X0, TRAY_Y0)
leds = union([cyl(x, y, 0.0, MTX_Z0, LED_BODY) for x, y in led_xy])
clash(f"{len(led_xy)} LEDs vs facade / pads / posts", leds)
# the opal acrylic, dropped in from behind onto the ledge
clash("opal acrylic disc",
      slab(half_disc(W / 2, CRES_Y, CRES_R + 0.2, ry=CRES_RY + 0.2), DIFF_LIP,
           DIFF_LIP + DIFF_T))
# The diffusion air gap must be clear or it is not a diffusion cavity. The six
# carrier pads are the ONE thing allowed into it, so they are subtracted from
# the envelope rather than waved through with an allowance -- that way the check
# still catches anything else that wanders in, and it fails if a pad moves
# somewhere it was not vetted for. How close each one comes to a pixel is
# measured separately, in the pad table.
_gap_env = slab(half_disc(W / 2, CRES_Y, CRES_R, ry=CRES_RY),
                DIFF_LIP + DIFF_REBATE, CAV_Z)
# Grown by a hair so the subtraction is watertight against the pad's own faces.
# NOT .scale() -- that scales about the ORIGIN, which slides the pads sideways by
# metres of x and leaves the real ones fully inside the envelope.
for _px, _py in pad_pts:
    _gap_env = _gap_env - carrier_pad_solid(_px, _py, grow=0.05)
clash("diffusion air gap (carrier pads excepted)", _gap_env)
# >>> AND PROVE THE PADS STAY INSIDE THE CAVITY. `pad_wall_margins()` is
# >>> arithmetic on a radius; this is the geometry itself. Intersect the built
# >>> pads with everything OUTSIDE the cavity's outer face -- it has to be zero.
# >>> The arithmetic version of this check measured the shaft radius, missed that
# >>> the base flare was 1.5 mm bigger, and cheerfully vouched for a boss sitting
# >>> 1.2 mm inside the dome's retaining-rib band.
_outside = (slab(outline2(), 0.0, CARRIER_Z0)
            - slab(half_disc(W / 2, CRES_Y, CAV_R, skirt=CAV_WALL, ry=CAV_RY),
                   -1.0, CARRIER_Z0 + 1.0))
clash("carrier pads stay inside the cavity wall",
      union([_ps ^ _outside for _ps in pad_solids]))
# each speaker body, plus the nubs sweeping in from behind
for _sx in (SPK_X, W - SPK_X):
    clash(f"speaker body @ x={_sx:.1f}",
          slab(rect2(_sx - SPK_BODY_W / 2, SPK_Y0, SPK_BODY_W, SPK_BODY_H),
               FP_T, FP_T + 22.0))
    for _ny, _w in ((SPK_Y0 - SPK_NUB_PROJ, "lower"), (SPK_Y1, "upper")):
        clash(f"  {_w} nub @ y={_ny:.1f}",
              slab(rect2(_sx - 4.0, _ny, 8.0, SPK_NUB_PROJ),
                   FP_T + SPK_NUB_Z, FP_T + SPK_NUB_Z + 6.0))
# the mic array board sitting in its channel, clear of the gasket lands
clash("mic array board (above the gasket lands)",
      slab(rect2(W / 2 - MIC_PCB_W / 2, MIC_Y0, MIC_PCB_W, MIC_PCB_H),
           MIC_Z0 + MIC_LAND_H, MIC_Z0 + MIC_LAND_H + 1.6),
      allow=2 * math.pi * (MIC_BOSS_D / 2) ** 2 * 1.6 + 1)   # the 2 M3 bosses
# The dome groove. The keep-out band is RIB_W wide -- the RIB is the part that
# grips the BACK face, which is the only face bosses stand off. (LIP_W is the
# front cover and is irrelevant here; the facade is flat.)
#
# The band follows the two FLANKS and the ARC but NOT the bottom edge: the
# bottom is the open end the module slides in through, and the bottom plate
# captures it there instead. The full flank height has to stay clear, because
# every point of it travels through the groove on the way up.
groove = (outline2() - outline2().offset(-RIB_W)) - rect2(
    REVEAL + RIB_W, BP_T - 1.0, W - 2 * (REVEAL + RIB_W), RIB_W + 1.0)
clash("dome groove band - flanks + arc must stay plain",
      slab(groove, FP_T, CAV_Z + 20.0))

# ---------------------------------------------------------------------------
# FEATURE PRESENCE
# ---------------------------------------------------------------------------
# The interference tests above are all NEGATIVE -- they prove nothing is where
# it shouldn't be. They cannot notice a retention feature that quietly vanished
# into a boolean. So probe for material where each one is supposed to BE.
say("")
say("feature presence (a 1 mm probe must find plastic)")


def probe(name, x, y, z, want=True, size=1.0):
    """Is there plastic at (x,y,z)? Tested with a cube of side `size`.

    >>> THE CUBE MUST BE SMALLER THAN THE FEATURE. A 1 mm probe is fine for
    >>> "is there a boss here", and useless for a 0.4 mm hook: the cube reaches
    >>> 0.5 mm in every direction, so at the hook it also samples the beam behind
    >>> it and the board gap in front. When the clip reach came down from 1.2 to
    >>> 0.4 the "clear below the back face" probes all flipped to solid -- not
    >>> because anything had grown into the board, but because the probe was now
    >>> wider than the clearance it was measuring. Small features get small cubes.
    """
    hit = (part_body ^ Manifold.cube((size, size, size))
           .translate((x - size / 2, y - size / 2, z - size / 2))).volume() > 1e-9
    ok = (hit == want)
    say(f"  {'FAIL' if not ok else 'ok  '} {'solid' if hit else 'empty':>6}   "
        f"{name}")
    if not ok:
        bad.append((name, -1))


for _sx in (SPK_X, W - SPK_X):
    side = "L" if _sx < W / 2 else "R"
    for _py, _w in ((SPK_Y0 - SPK_FIT - (SPK_NUB_PROJ+SPK_POST_WALL)/2, "lower"),
                    (SPK_Y1 + SPK_FIT + (SPK_NUB_PROJ+SPK_POST_WALL)/2, "upper")):
        probe(f"speaker {side} {_w} nub post", _sx, _py, FP_T + 1.0)
    # >>> THE OLD "left / right locating rib" PROBES ARE GONE. There are no
    # >>> flank ribs on the rotated mount -- two screws top and bottom locate the
    # >>> body completely. The probes survived the rotation and passed by
    # >>> accident, hitting the stiffening rib that used to run at SPK_Y.
    #
    # What has to be checked instead is the OUTBOARD flank, and checked the
    # other way round: it must be BARE. The width chain budgets SPK_FLANK = 1.0
    # there and nothing else, and it butts straight onto the dome's retaining-rib
    # keep-out -- so anything that appears in that 1 mm jams the module on
    # assembly. Probe the middle of the gap.
    #
    # The INBOARD flank is deliberately not probed either way: the matrix end
    # clip lives in that band by design, and how close it comes to the speaker
    # seat is measured properly in the clearance table.
    _fo = _sx - (SPK_BODY_W/2 + SPK_FLANK/2) if _sx < W/2 else \
          _sx + (SPK_BODY_W/2 + SPK_FLANK/2)
    probe(f"speaker {side} OUTBOARD flank stays bare", _fo, SPK_Y, FP_T + 2.0,
          want=False)
# >>> PROBE THE PAD DOWN ITS WHOLE HEIGHT, NOT JUST AT THE TOP. The first
# >>> version sampled once at CARRIER_Z0 - 1.0 and passed while the pad was a
# >>> 1.13 mm stub floating over a hole -- the bore had eaten everything below.
# >>> A single probe near a feature's tip cannot tell a boss from a lid.
for _px, _py, _deg in carrier_pads():
    _pxx, _pyy = W/2 + _px, CRES_Y + _py
    # Sample between PAD_Z0 (the pocket floor it starts on) and the seat -- not
    # from z=0, which is inside the acrylic pocket where the pad is absent BY
    # DESIGN and a probe would fail for the wrong reason.
    _pz0, _pz1 = PAD_Z0 + PAD_RAMP + 0.5, CARRIER_Z0 - 0.5
    for _f, _lab in ((0.05, "at the seat"), (0.50, "mid-height"),
                     (0.95, "just above the ramp")):
        probe(f"carrier pad @ {_deg:.0f} deg, {_lab}",
              _pxx + PAD_W*0.30, _pyy, _pz1 - _f * (_pz1 - _pz0))
    # ...and the pilot must be a HOLE through that solid, to its full depth
    probe(f"  ...pilot open to depth @ {_deg:.0f} deg", _pxx, _pyy,
          CARRIER_Z0 - PAD_PILOT_Z + 0.5, want=False)
    # ...but must NOT break through into the air gap below it
    probe(f"  ...pilot bottoms out @ {_deg:.0f} deg", _pxx, _pyy,
          CARRIER_Z0 - PAD_PILOT_Z - 1.0)
# >>> NO FLOATING LAYER IN THE RAMP. "connected bodies == 1" does NOT catch this:
# >>> a tip hanging in mid-air is still joined to the shaft above it, so the part
# >>> stays one body while its first layers print into nothing. The ramp exists to
# >>> grow the pad OUT OF the wall, so the test is that every height in it has
# >>> material AT the wall's inner face -- attached, not merely nearby.
for _px, _py, _deg in carrier_pads():
    _x, _y = W/2 + _px, CRES_Y + _py
    _ox, _oy = _pad_axis(_x, _y)
    for _f in (0.08, 0.4, 0.75):
        _z = PAD_Z0 + PAD_RAMP * _f
        probe(f"pad @ {_deg:.0f} deg ramp touches the wall at z={_z:.1f}",
              _x + _ox * PAD_OFFSET_IN, _y + _oy * PAD_OFFSET_IN, _z)
# >>> PROBE THE RIB, NOT THE BAND. These sampled the band's midpoint, which was
# >>> solid only because the old pad filled the whole band. A rib occupies a
# >>> slice of it, so the probe has to know where the rib actually is.
probe("stiffening rib (above matrix)", W / 2,
      (SPINE_Y0 + SPINE_Y1) / 2, FP_T + RIB_H - 1.0)
for _i, _sy2 in enumerate(_rib2_y):
    probe(f"stiffening rib {_i} (below matrix)", W / 2,
          _sy2 + RIB_T / 2, FP_T + RIB_H - 1.0)
if len(_rib2_y) == 2:
    probe("...and they are two SEPARATE ribs", W / 2,
          (_rib2_y[0] + RIB_T + _rib2_y[1]) / 2, FP_T + RIB_H - 1.0, want=False)
# ...and the band between ribs must now be OPEN, which is the whole point
probe("band above the matrix is no longer a solid pad", W / 2,
      SPINE_Y0 + 0.8, FP_T + RIB_H - 1.0, want=False)
probe("cavity wall at the apex", W / 2, CRES_Y + DIFF_RY + CAV_WALL / 2, CAV_Z - 1)
_clip_spec = ([(f"bottom {i}", "y", mtx_y0, -1, cx)
                 for i, cx in enumerate(CLIP_BOT_X)]
              + [(f"top {i}", "y", mtx_y1, +1, cx)
                 for i, cx in enumerate(CLIP_TOP_X)])
for _nm, _ax, _face, _sg, _ctr in _clip_spec:
    if _ax == "x":
        beam = (_face + _sg * (CLIP_GAP + CLIP_T / 2), _ctr)
        hook = (_face - _sg * (CLIP_ENGAGE / 2), _ctr)
    else:
        beam = (_ctr, _face + _sg * (CLIP_GAP + CLIP_T / 2))
        hook = (_ctr, _face - _sg * (CLIP_ENGAGE / 2))
    # >>> PROBED AT THE STACK'S BACK FACE, WHICH IS WHERE THE HOOK NOW IS. These
    # >>> three sampled MTX_ZB, the matrix board's back -- correct while the clip
    # >>> gripped there, and silently wrong the moment it moved back to grip the
    # >>> whole sandwich. All three then reported the hook "empty", which is true
    # >>> of that plane and says nothing about whether the hook exists.
    _fine = CLIP_REACH / 3.0          # smaller than the feature under test
    probe(f"clip {_nm} beam", beam[0], beam[1], BP_ZB - 1.0)
    # the hook must overhang the stack, ABOVE its back face...
    # >>> SAMPLED NEAR THE TIP OF THE 45 deg FACET, not half way up it. The
    # >>> retaining face slopes from the beam's inner face to the hook tip across
    # >>> CLIP_RUN, so at mid-height it has only reached half the engagement --
    # >>> probing there for the full overlap reports "empty" on a hook that is
    # >>> perfectly present.
    probe(f"clip {_nm} hook (over the stack)", hook[0], hook[1],
          BP_ZB + CLIP_STACK_CLR + CLIP_RUN * 0.95, size=_fine)
    # ...and must NOT be inside the stack below that face
    probe(f"clip {_nm} clear below the back face", hook[0], hook[1],
          BP_ZB - 0.8, want=False, size=_fine)
for _i, (_px, _py) in enumerate(mtx_posts):
    probe(f"matrix locating post {_i}", _px, _py, MTX_Z0 + MTX_PCB_T / 2)
# (seating pads retired -- the board lands on the facade lip; see the note
#  where they used to be built. Their positions are still tracked for the
#  drawings and the interference check.)
for _i, (_px, _py) in enumerate([] if MTX_STANDOFF == 0.0 else mtx_pads):
    probe(f"matrix seating pad {_i}", _px, _py, FP_T + MTX_STANDOFF / 2)
for _mx in mic_x():
    probe(f"gasket land @ x={_mx:.1f}", _mx + (MIC_PORT_D + MIC_GASKET) / 2,
          MIC_Y, MIC_Z0 + MIC_LAND_H / 2)
# >>> THE LIP IS A PERFORATED SHEET NOW, not a frame round an open hole, so the
# >>> board seats on it across the whole field. Probe a WEB between two windows.
probe("facade web between two LED windows (the board seats on it)",
      (led_xy[0][0] + led_xy[MTX_LED_ROWS][0]) / 2, led_xy[0][1],
      MTX_INSET / 2, size=0.3)
# >>> AND THE WINDOWS THEMSELVES MUST BE OPEN. This used to assert the single
# >>> aperture was clear at its centre; there are 288 windows now, so check that a
# >>> window is open AND that its neighbour web is solid -- the pair is what says
# >>> the grid actually got cut rather than the whole area being removed.
probe("an LED window is open through the lip", led_xy[0][0], led_xy[0][1],
      MTX_INSET / 2, want=False, size=0.3)

# --- the pin gutters -------------------------------------------------------
# >>> PROBED IN THREE PLACES, because any one of them alone is satisfiable by the
# >>> wrong solid: an open gutter that has eaten through the facade, an intact
# >>> facade with no gutter behind it, and a gutter that has undercut a post all
# >>> look fine from one probe.
say("")
_gz_mid = MTX_INSET - MTX_GUTTER_D / 2
for _i, (_gy0, _gy1) in enumerate(MTX_GUTTERS):
    _nm = "bottom" if _i == 0 else "top"
    _gy = (_gy0 + _gy1) / 2
    # somewhere along the run that is clear of every post pedestal
    _gx = MTX_X0 + TRAY_W / 2
    probe(f"{_nm} pin gutter is open behind the facade", _gx, _gy, _gz_mid,
          want=False, size=0.3)
    probe(f"{_nm} pin gutter has NOT broken through the facade", _gx, _gy,
          (MTX_INSET - MTX_GUTTER_D) / 2, size=0.3)
for _i, (_px, _py) in enumerate(mtx_posts):
    probe(f"post {_i} still stands on solid lip (pedestal)", _px, _py, _gz_mid,
          size=0.3)

# --- the LED crescent's wire exit -------------------------------------------
# >>> FOUR PROBES, because "there is a hole there" is not the requirement. The hole
# >>> must be open, the bar must SURVIVE below it (or the wall is gone and the
# >>> carrier has nothing to seat on), and the FACADE must be untouched -- a cut
# >>> that reached z=0 would put a 10 x 5 window in the front of the machine.
# >>> AND WHILE CUTTING THAT BAR, A CLASH THAT WAS ALREADY THERE. strip_rects()
# >>> says it in its own docstring -- the RIBBON is STRIP_W (10) tall against the
# >>> LED's 5.2, so it reaches 2.4 mm further up and down than any pixel. That note
# >>> was written about pads at the APEX. The same 2.4 mm at the BOTTOM row runs
# >>> straight into this bar: the rows are placed so the lowest pixel's edge grazes
# >>> the aperture's flat bottom at CRES_Y, which leaves the ribbon hanging 2.4 mm
# >>> BELOW the cavity floor, where the bar is solid.
# >>> THIS PART REACHES INTO THE DOME, AND NOTHING WAS CHECKING IT. The crescent
# >>> baffle runs CARRIER_Z0 back from the facade, so the first ~19 mm of the
# >>> dome's interior is not free space -- but the encoder and ToF hang from the
# >>> crown at a depth chosen before the baffle existed, and had 77.8 and 55.4 mm^3
# >>> of board buried in it. Neither part could see it: the dome checks its own
# >>> features, this file checks its own, and the interference lived between them.
# >>> The intruding part is the right place for the check, because it is the one
# >>> that knows how far it reaches.
say("")
say("crown boards (dome-mounted) vs this module's reach")
# >>> AND "THIS MODULE" MEANS THE STACK ON IT, NOT JUST THE MOULDING. The first
# >>> version of this check compared the crown boards against part_body alone and
# >>> reported 0.00 -- while the encoder board was actually 0.50 mm inside the LED
# >>> CARRIER, which is a different STL and so invisible to it. The carrier bolts to
# >>> this part's cavity wall and its screw heads stand up off that; from the crown
# >>> boards' point of view all three are one obstacle. Model the stack.
_carrier_env = slab(half_disc(W / 2, CRES_Y, CAV_R_G, skirt=CARRIER_SKIRT,
                             ry=CAV_RY_G),
                    CARRIER_Z0, CARRIER_Z0 + CARRIER_T + CARRIER_SCREW_H)
_stack = part_body + _carrier_env
say(f"            (the stack reaches {CARRIER_Z0 + CARRIER_T + CARRIER_SCREW_H:.2f}: "
    f"cavity wall {CARRIER_Z0:.2f} + carrier {CARRIER_T} + screw head "
    f"{CARRIER_SCREW_H})")
for _cnm, _ccx, _ccz, _cbw, _cbd, _coffs, _cstand in crown_boards():
    _ctip = min(crown_inner_y(_ccx + _dx) for _dx, _ in _coffs) - _cstand
    _cenv = Manifold.cube((_cbw, 1.6 + 6.0, _cbd)).translate(
        (_ccx - _cbw / 2, _ctip - 1.6 - 6.0, _ccz - _cbd / 2))
    _v = (_stack ^ _cenv).volume()
    say(f"  {'FAIL' if _v > 1e-6 else 'ok  '} {_v:9.2f}   {_cnm} board "
        f"(depth {_ccz - _cbd/2:.1f}-{_ccz + _cbd/2:.1f}) is clear of the "
        f"module AND the carrier stack on it")
    if _v > 1e-6:
        bad.append((f"{_cnm} board fouls the stack", -1))
# >>> REPORTED AGAINST THE STACK, not the baffle -- quoting the gap to the baffle
# >>> next to a clearance measured from the stack invites reading one as the other.
_stack_z = CARRIER_Z0 + CARRIER_T + CARRIER_SCREW_H
say(f"  ---- {min(c - _cbd / 2 for _n, _x, c, _w, _cbd, _o, _s in crown_boards()) - _stack_z:8.2f}"
    f"   nearest crown board to the stack top at z={_stack_z:.2f} "
    f"(design clearance {CROWN_CLR})")

say("")
say("LED ribbons vs the cavity bar")
for _i, (_hl, _ry, _hw) in enumerate(strip_rects()):
    _env = Manifold.cube((2 * _hl, 2 * _hw, CARRIER_Z0 - CAV_Z)).translate(
        (W / 2 - _hl, CRES_Y + _ry - _hw, CAV_Z))
    clash(f"row {_i} ribbon (y {CRES_Y+_ry-_hw:.1f}-{CRES_Y+_ry+_hw:.1f}) "
          f"is clear of the shell", _env)

say("")
_wx = (W / 2 - CAV_R + W / 2 - DIFF_R) / 2          # mid-thickness of the flank
_wz = CARRIER_Z0 - LED_WIRE_D / 2
probe("crescent wire exit is open through the LEFT flank",
      _wx, (LED_WIRE_Y0 + LED_WIRE_TOP) / 2, _wz, want=False, size=0.6)
probe("...the flank is solid ABOVE the exit (wall not severed)",
      _wx + 0.2, LED_WIRE_TOP + 2.0, _wz, size=0.6)
probe("...and solid deeper down, so this is a notch not a through-slot",
      _wx, (LED_WIRE_Y0 + LED_WIRE_TOP) / 2, LED_WIRE_Z0 - 1.5, size=0.6)
probe("...and the FACADE is untouched -- nothing shows from the front",
      _wx, (LED_WIRE_Y0 + LED_WIRE_TOP) / 2, FP_T / 2, size=0.6)
# >>> ANCHORED TO baffle_floor(), NOT TO CRES_Y. This probed a fixed
# >>> y = CRES_Y - CAV_WALL/2, which was the middle of the bar back when the floor
# >>> was flat. The floor is drafted now and has dropped 2.78 mm by this depth, so
# >>> the old point sits in open cavity and the probe failed -- correctly reporting
# >>> "air", about a place that is supposed to be air. The floor moved; the probe
# >>> has to move with it.
probe("...and the cavity FLOOR is whole -- no bottom material removed",
      _wx, baffle_floor(_wz) - CAV_WALL / 2, _wz, size=0.6)
# >>> PICKED BY DISTANCE IN BOTH AXES. Choosing on |y - exit_y| alone selected the
# >>> pad at dx = +89.19 -- the one on the RIGHT flank -- because the left and right
# >>> pads share the same y and min() simply took the first. Identical mistake to
# >>> the coupon's `_cx in CLIP_TOP_X`: a key that cannot tell the two candidates
# >>> apart. The exit is on the LEFT, so x has to be in the key.
_ex, _ey = (LED_WIRE_X0 + LED_WIRE_X1) / 2, LED_WIRE_Y0 + LED_WIRE_H / 2
_pad_lo = min(carrier_pads(),
              key=lambda p: ((W / 2 + p[0]) - _ex) ** 2
              + ((CRES_Y + p[1]) - _ey) ** 2)
_pad_lo_y = CRES_Y + _pad_lo[1]
_pad_trim = max(0.0, LED_WIRE_TOP - (_pad_lo_y - PAD_W / 2))
_pilot_wall = (_pad_lo_y - PAD_PILOT_D / 2) - LED_WIRE_TOP
# >>> PROBED BESIDE THE PILOT, NOT AT IT. The pilot is a HOLE: probing its centre
# >>> for solid material asserts the screw hole was never drilled, and duly failed.
# >>> What matters is the wall between the trim edge and the pilot bore.
probe("...wall survives between the trim edge and the pad's pilot",
      W / 2 + _pad_lo[0], _pad_lo_y - PAD_PILOT_D / 2 - 0.4, CARRIER_Z0 - 0.5,
      size=0.4)
say(f"pad trim    {_pad_trim:.2f} mm off the {_pad_lo[2]:.0f} deg pad, "
    f"{_pilot_wall:.2f} mm of wall left beside its pilot")
say(f"wire exit   {LED_WIRE_D:.0f} deep, {LED_WIRE_H:.2f} wide at the front of the "
    f"slot and {LED_WIRE_H_DEEP:.2f} at the back (its floor follows the baffle "
    f"draft); LEFT flank, x~{_wx:.1f}, top y {LED_WIRE_TOP:.2f}, "
    f"z {LED_WIRE_Z0:.1f}-{CARRIER_Z0:.1f}")
if LED_WIRE_TOP < CRES_Y + LED_WIRE_H_WANT - BAFFLE_DROP - 1e-6:
    say(f"            (asked for {LED_WIRE_H_WANT:.0f} wide; capped by the "
        f"{_pad_lo0[2]:.0f} deg pad's screw pilot)")

# --- the grid's boundary walls, and what the gutters have left ---------------
_ymin_led = min(y for _, y in led_xy)
_ymax_led = max(y for _, y in led_xy)
# >>> MEASURED IN THE SOLID, not computed from MTX_GUTTER_WEB. Now that the web is
# >>> DERIVED from the pitch, "web == inner web" is true by construction and a
# >>> check that compares the two constants can only ever print 0.00 -- the same
# >>> self-referential trap the facade-thickness check fell into. Walking the body
# >>> can still disagree: if a gutter overran and merged with the outermost row of
# >>> windows, the wall would be gone and only the solid would know.
def _wall_span(x, y_start, direction, z, limit=3.0, step=0.02):
    """March from y_start while material lasts; return how far it lasted."""
    d = 0.0
    while d < limit:
        _c = Manifold.cube((0.15, step, 0.15)).translate(
            (x - 0.075, y_start + direction * (d + step / 2) - step / 2,
             z - 0.075))
        if (part_body ^ _c).volume() <= 1e-9:
            break
        d += step
    return d


_xcol = led_xy[0][0]                      # an LED column, so we hit a window
_web_bot = _wall_span(_xcol, MTX_GUTTERS[0][1], +1, MTX_INSET / 2)
_web_top = _wall_span(_xcol, MTX_GUTTERS[1][0], -1, MTX_INSET / 2)
_gut_w_bot = MTX_GUTTERS[0][1] - MTX_GUTTERS[0][0]
_gut_w_top = MTX_GUTTERS[1][1] - MTX_GUTTERS[1][0]
say("")
say(f"grid edges  perimeter web {_web_bot:.3f} bottom / {_web_top:.3f} top, "
    f"against {MTX_LED_PITCH - MTX_WINDOW:.3f} between every inner cell")
say(f"            gutters left {_gut_w_bot:.2f} / {_gut_w_top:.2f} wide, "
    f"a 0.1\" row sits {MTX_PIN_ROW_BAND[0]}-{MTX_PIN_ROW_BAND[1]} from the edge")

# --- how thick is the facade in front of a gutter, really? -------------------
# >>> WALK THE SOLID. Sampling z from the facade backwards at the gutter centre and
# >>> finding where material stops is the only version of this that can disagree
# >>> with the constants -- which is the entire point of measuring it.
_fx, _fy = MTX_X0 + TRAY_W / 2, (MTX_GUTTERS[0][0] + MTX_GUTTERS[0][1]) / 2
_facade_measured = 0.0
_step = 0.025
_z = _step / 2
while _z < MTX_INSET + 0.5:
    _c = Manifold.cube((0.2, 0.2, _step)).translate(
        (_fx - 0.1, _fy - 0.1, _z - _step / 2))
    # >>> part_body, NOT body. They differ by the STL export shift (-REVEAL, -BP_T),
    # >>> and reading the wrong one put this probe 2.5 mm sideways into solid lip,
    # >>> where it cheerfully measured the full 1.40 and passed -- while the probe
    # >>> three lines above, which does use part_body, said the gutter was open.
    # >>> Two measurements of the same point disagreeing is the only reason it got
    # >>> noticed.
    if (part_body ^ _c).volume() > 1e-9:
        _facade_measured = _z + _step / 2
        _z += _step
    else:
        break
say("")
say(f"gutter      facade measures {_facade_measured:.3f} mm in front of the "
    f"bottom gutter (design {MTX_INSET - MTX_GUTTER_D:.2f})")

# >>> THE WEB BETWEEN THE GUTTER AND THE LAST WINDOW IS READ OFF THE SOLID, not
# >>> recomputed from the constants that built it. The obvious version --
# >>> "gutter_edge is MTX_GUTTER_WEB from the window edge" -- is the construction
# >>> restated, and it passes even if the gutter overran and merged with the bottom
# >>> row of windows. Probe the web instead: if the two ran together, it is air.
_lowest = min(y for _, y in led_xy)
probe("web survives between the bottom gutter and the first LED window",
      led_xy[0][0], (MTX_GUTTERS[0][1] + (_lowest - MTX_WINDOW / 2)) / 2,
      _gz_mid, size=0.2)
_highest = max(y for _, y in led_xy)
probe("web survives between the top gutter and the last LED window",
      led_xy[0][0], (MTX_GUTTERS[1][0] + (_highest + MTX_WINDOW / 2)) / 2,
      _gz_mid, size=0.2)

# ---------------------------------------------------------------------------
# THE SPLIT
# ---------------------------------------------------------------------------
say("")
if not NEEDS_SPLIT:
    say(f"split       NOT NEEDED -- {W-2*REVEAL:.1f} x {H-REVEAL-BP_T:.1f} fits "
        f"the {BED:.0f} bed whole, {BED-(W-2*REVEAL):.1f} / "
        f"{BED-(H-REVEAL-BP_T):.1f} mm to spare")
else:
    _lb, _rb = left_part.bounding_box(), right_part.bounding_box()
    _lw, _lh = _lb[3] - _lb[0], _lb[4] - _lb[1]
    _rw, _rh = _rb[3] - _rb[0], _rb[4] - _rb[1]
    say(f"split       seam x={SPLIT_X}, {LAP_W} lap stepped at z={LAP_Z}, "
        f"{LAP_CLR} clearance, {len(PEG_Y)} alignment pegs")
    say(f"  front-module-L.stl  {_lw:6.2f} x {_lh:6.2f} x {_lb[5]-_lb[2]:5.2f}   "
        f"{left_part.volume()/1000:5.1f} cm3")
    say(f"  front-module-R.stl  {_rw:6.2f} x {_rh:6.2f} x {_rb[5]-_rb[2]:5.2f}   "
        f"{right_part.volume()/1000:5.1f} cm3")

    # The two halves must ADD BACK UP. Re-union them (with the pegs removed from the
    # comparison, since they are new material) and the only difference from the
    # whole part should be the joint clearance -- a thin film, not a chunk.
    _rejoin = left_part + right_part
    _lost = (body - _rejoin).volume()
    _gain = (_rejoin - body).volume()
    split_checks = [
        ("L fits the bed in x", BED - _lw),
        ("L fits the bed in y", BED - _lh),
        ("R fits the bed in x", BED - _rw),
        ("R fits the bed in y", BED - _rh),
        # Rejoined, the halves must reproduce the whole part: the only material
        # missing is the clearance film along the seam, and NOTHING may be gained
        # (the pegs are reassigned material, not new -- they sit inside the original
        # plate and are matched by holes in the other half).
        ("rejoined loses only the clearance film", 400.0 - _lost),
        ("rejoined gains nothing", 0.01 - _gain),
        # the seam must miss every boss, or a boss ends up in two halves
        ("seam clear of the L speaker seat",
         (SPLIT_X - LAP_W/2) - (SPK_X + SPK_BODY_W/2 + SPK_SEAT_W)),
        ("seam clear of the matrix end clip",
         (mtx_x0 - CLIP_GAP - CLIP_T) - (SPLIT_X + LAP_W/2)),
        ("whole clock is on ONE piece", mtx_x0 - (SPLIT_X + LAP_W/2)),
        # A boss stands on the facade. If the lap plane runs between a boss and the
        # material it stands on, the boss ends up floating on the wrong half -- so
        # every boss has to sit clear of the lap in x.
        ("mic boss clear of the lap",
         (W/2 - MIC_BOSS_X - MIC_BOSS_D/2) - (SPLIT_X + LAP_W/2)),
    ]
    for _nm, _v in split_checks:
        say(f"  {'FAIL' if _v < 0 else 'ok  '} {_v:8.2f}   {_nm}")
    bad += [c for c in split_checks if c[1] < 0]
    say(f"  (rejoin: {_lost:.1f} mm3 lost to clearance, {_gain:.1f} gained)")


    # A peg is only doing its job if the LEFT half has material there above the lap
    # plane AND the RIGHT half has a hole to receive it. Check both, per peg.
    def _in(solid, x, y, z):
        return (solid ^ Manifold.cube((0.8, 0.8, 0.8))
                .translate((x - 0.4, y - 0.4, z - 0.4))).volume() > 1e-6


    for _i, _py in enumerate(PEG_Y):
        _z = LAP_Z + PEG_H / 2
        _pl = _in(left_part.translate((REVEAL, BP_T, 0)), SPLIT_X, _py, _z)
        _pr = _in(right_part.translate((REVEAL, BP_T, 0)), SPLIT_X, _py, _z)
        ok = _pl and not _pr
        say(f"  {'FAIL' if not ok else 'ok  '}   peg {_i} @ y={_py:5.1f}   "
            f"L={'solid' if _pl else 'empty'}  R={'empty' if not _pr else 'SOLID'}")
        if not ok:
            bad.append((f"peg {_i}", -1))

# ---- checks ---------------------------------------------------------------
say("")
checks = [
    ("clip clear of the speaker seat",
     (mtx_x0 - CLIP_GAP - CLIP_T) - (SPK_X + SPK_BODY_W / 2 + SPK_SEAT_W)),
    ("room below the matrix for its clip",
     (mtx_y0 - CLIP_GAP - CLIP_T) - BP_T),
    ("room above the matrix for its clip",
     (MIC_Y0 - MIC_FIT) - (mtx_y1 + CLIP_GAP + CLIP_T)),
    # There is no speaker rib any more -- the tallest thing above the body is the
    # NUB POST, SPK_POST_H_Y (6.0) not SPK_RING_W (3.0). Measuring the rib made
    # this read 3 mm more clearance than the part actually has.
    ("cavity wall clear of the speaker post",
     (CRES_Y - CAV_WALL) - (SPK_Y1 + SPK_FIT + SPK_POST_H_Y)),
    ("cavity wall clear of the mic channel", (CRES_Y - CAV_WALL) - MIC_Y1),
    # --- LED carrier interface ---------------------------------------------
    # Equality, not an inequality: the wall's back face must land EXACTLY one
    # strip thickness behind the LED plane, or the carrier either crushes the
    # ribbon or leaves it floating. Written as -abs(...) like the nub-plane check
    # above, so float noise on an exact zero does not read as a failure.
    ("carrier seat lands on the strip back (must be 0)",
     0.001 - abs(CARRIER_Z0 - CAV_Z - LED_STRIP_T)),
    ("pilot stays out of the acrylic pocket",
     (CARRIER_Z0 - PAD_PILOT_Z) - (DIFF_LIP + DIFF_REBATE)),
    ("tightest pad -> nearest pixel", min(c for _, c in pad_led_clearances())),
    # The SHAFT -- the part the screw goes into -- must clear the wall's outer
    # face on its own. The base flare is deliberately clipped flush by the
    # cavity envelope (see carrier_pad_solid), and how much gets taken is
    # reported separately below; that is a gusset, not structure.
    ("tightest pad SHAFT inside the wall outer face",
     min(m for _, m in pad_wall_margins())),
    ("mic boss clear of the array end", MIC_PCB_W / 2 - MIC_BOSS_X),
    ("facade left in front of the acrylic", DIFF_LIP),
    ("acrylic pocket vs 3.0 acrylic", DIFF_REBATE - DIFF_T),
    # the nub's landing face is SPK_NUB_Z behind the speaker's front face, and
    # that front face sits on the back of the facade -- so the post top must
    # land exactly on FP_T + SPK_NUB_Z or the nub is pre-loaded / floating
    ("post top on the nub plane (must be 0)",
     -abs((FP_T + SPK_NUB_Z) - (FP_T + SPK_NUB_Z))),
    ("pilot stays inside the post", SPK_NUB_Z - SPK_PILOT_Z),
    ("cavity wall clear of the module edge", (ARCH_R - REVEAL) - CAV_R),
    ("cavity wall clear of the module top", (ARCH_RY - REVEAL) - CAV_RY),
    ("part fits a 256 mm bed (x)", 256.0 - (W - 2 * REVEAL)),
    ("part fits a 256 mm bed (y)", 256.0 - (H - REVEAL - BP_T)),
    ("bbox x == the module outline", 0.01 - abs(bb[3] - bb[0] - (W - 2*REVEAL))),
    ("bbox y == the module outline", 0.01 - abs(bb[4] - bb[1] - (H - REVEAL - BP_T))),
    ("nothing trimmed by the containment guard", 0.01 - trimmed),
    ("spine clear of the matrix clips", SPINE_Y0 - (TRAY_Y1 + CLIP_GAP + CLIP_T)),
    # >>> THE CLIP MUST SURVIVE BEING SPRUNG -- a STRESS check, in a file that had
    # >>> only ever asked about CLEARANCE. Peak strain in a straight cantilever is
    # >>> 1.5*t*y/L^2: thickness x deflection over the SQUARE of free length. The
    # >>> original clip (t=2.2, y=1.2, L=2.2) came to 82 %, against ~2 % for PLA.
    # >>> Nothing caught it because a clip that cannot bend still fits perfectly.
    # the deflection to assemble is the ENGAGEMENT -- how far the hook tip has to
    # travel back to reach the board's edge -- not the reach from the beam.
    ("clip strain is within " + CLIP_MAT,
     CLIP_STRAIN_MAX - 1.5 * CLIP_T * CLIP_ENGAGE
     / (BP_ZB + CLIP_STACK_CLR - CLIP_ROOT_Z + CLIP_RUN) ** 2),
    # ...and it must still grip: this used to test CLIP_REACH, which is measured
    # from the beam and so passed while the real overlap was 0.15 mm.
    ("clip actually overlaps the stack (>=0.3)", CLIP_ENGAGE - 0.3),
    ("clip overlap is under a third of the board edge",
     MTX_BP_T / 3.0 - CLIP_ENGAGE),
    # >>> AND NOTHING MAY SIT ON A CONNECTOR. Ø of this was checked before: the
    # >>> end clips were built straight onto the driver's STEMMA QT ports, which
    # >>> gen_tray.py has notched around since it was written. The keep-out is
    # >>> that notch, taken from the same number.
    ("no clip on the STEMMA QT end ports (none on the ends at all)",
     0.0 if not any(_a == "x" for _a in _CLIP_AXES) else -1.0),
    ("gap between the two lower ribs is printable",
     (_rib2_y[1] - (_rib2_y[0] + RIB_T)) - RIB_MIN_GAP if len(_rib2_y) == 2
     else 0.0),
    ("spine clear of the speaker tops", SPK_Y1 - SPINE_Y1),
    ("spine clear of the speakers (x)", SPINE_X0 - (SPK_X + SPK_BODY_W/2 + SPK_FIT)),
    # --- the pin gutters, and what they cost --------------------------------
    # >>> MEASURED OFF THE SOLID, NOT RESTATED. The version of this check that read
    # >>> (MTX_INSET - MTX_GUTTER_D) - MTX_FACADE_MIN reported "ok 0.00" the moment
    # >>> MTX_INSET became the sum of those two terms -- it was subtracting a number
    # >>> from itself and could never fail again. _facade_measured walks the actual
    # >>> body from the facade backwards and finds where material stops.
    (f"facade in front of a gutter, MEASURED {_facade_measured:.2f} "
     f"(>= {MTX_FACADE_MIN})", _facade_measured - MTX_FACADE_MIN),
    ("gutter is deeper than the trimmed pin it has to swallow",
     MTX_GUTTER_D - MTX_PIN_H),
    # >>> THE PEDESTAL MUST REACH THE LIP THAT REMAINS. A post 1.905 mm from the
    # >>> board edge, with a collar smaller than the gutter is wide, would stand on
    # >>> an ISLAND inside the gutter -- touching at a tangent, so still "one body"
    # >>> in the boolean, but held on by nothing you could print.
    (f"post pedestal reaches past the gutter into solid lip "
     f"(r={MTX_POST_D/2 + MTX_POST_COLLAR:.2f})",
     (MTX_HOLES[0][1] + MTX_POST_D / 2 + MTX_POST_COLLAR)
     - (MTX_GUTTERS[0][1] - TRAY_Y0)),
    ("LED plane is closer to the facade than the pins used to hold it",
     (MTX_INSET + MTX_PIN_H) - MTX_INSET - 0.001),
    # >>> THE BOUNDARY CELLS MUST BE WALLED LIKE THE INNER ONES. Measured off the
    # >>> solid, then compared to the INNER web -- not to a threshold of its own.
    # >>> A number of its own is how the perimeter came to be 0.30 against 0.74
    # >>> inside: it passed every check because nothing ever compared the two.
    (f"bottom perimeter web {_web_bot:.3f} >= inner web "
     f"{MTX_LED_PITCH - MTX_WINDOW:.3f}",
     _web_bot - (MTX_LED_PITCH - MTX_WINDOW) + 1e-9),
    (f"top perimeter web {_web_top:.3f} >= inner web "
     f"{MTX_LED_PITCH - MTX_WINDOW:.3f}",
     _web_top - (MTX_LED_PITCH - MTX_WINDOW) + 1e-9),
    # ...and the wall must not have eaten the gutter it borders.
    (f"bottom gutter still covers a 0.1\" header row "
     f"({_gut_w_bot:.2f} wide)", _gut_w_bot - MTX_PIN_ROW_BAND[1]),
    (f"top gutter still covers a 0.1\" header row "
     f"({_gut_w_top:.2f} wide)", _gut_w_top - MTX_PIN_ROW_BAND[1]),
    # --- the crescent wire exit ---------------------------------------------
    ("wire exit leaves flank below it (bridges over the notch on print)",
     (LED_WIRE_Z0 - FP_T) - 1.0),
    ("wire exit floor never dips below the baffle floor",
     min(LED_WIRE_Y0 - baffle_floor(LED_WIRE_Z0),
         LED_WIRE_Y0_DEEP - baffle_floor(CARRIER_Z0)) + 1e-9),
    # >>> A REAL BOX-TO-BOX CLEARANCE. The first version only compared x, and only
    # >>> when the pad was within PAD_W in y -- so for every real pad it fell
    # >>> through to a 99.0 sentinel and printed "ok 99.00" without comparing
    # >>> anything. A check whose pass value is a constant it made up is not a
    # >>> check. Two boxes clear if they clear in EITHER axis, so take the better
    # >>> gap per pad and the worst of those.
    # >>> THE PAD TRIM IS BOUNDED, NOT FORBIDDEN. Butting into the lowest fixing pad
    # >>> is a deliberate trade -- the alternative is a shorter exit or a hole in
    # >>> the cavity floor, and neither is wanted. So the check does not demand
    # >>> clearance; it demands the trim stay small and, far more importantly, stay
    # >>> away from the pad's PILOT HOLE. A screw needs wall all round it, and that
    # >>> is the thing a growing exit would quietly eat.
    (f"pad trim is at most {LED_WIRE_PAD_TRIM_MAX} mm "
     f"(actually {_pad_trim:.2f})", LED_WIRE_PAD_TRIM_MAX - _pad_trim),
    (f"wall left beside the trimmed pad's pilot "
     f"({_pilot_wall:.2f} >= {PAD_PILOT_WALL_MIN})",
     _pilot_wall - PAD_PILOT_WALL_MIN),
    ("wire exit fully crosses the flank (it leans with the ellipse)",
     (LED_WIRE_X1 - LED_WIRE_X0) - CAV_WALL - 1.0),
]
bad += [c for c in checks if c[1] < 0]
for nm, v in checks:
    say(f"  {'FAIL' if v < 0 else 'ok  '} {v:7.2f}   {nm}")

try:
    import numpy as np
    import trimesh
    tm = trimesh.Trimesh(vertices=np.asarray(V), faces=np.asarray(F),
                         process=False)
    say("")
    say(f"watertight={tm.is_watertight}  winding_ok={tm.is_winding_consistent}  "
        f"volume={tm.volume/1000:.1f} cm^3  euler={tm.euler_number}")
    if not tm.is_watertight or not tm.is_winding_consistent:
        bad.append(("mesh not printable", -1))
    # split() needs scipy/networkx; fall back to a vertex-weld flood fill so a
    # floating feature can never slip through unnoticed
    try:
        nb = len(tm.split(only_watertight=False))
    except Exception:
        parent = list(range(len(tm.vertices)))

        def find(i):
            while parent[i] != i:
                parent[i] = parent[parent[i]]
                i = parent[i]
            return i

        for tri in tm.faces:
            a = find(int(tri[0]))
            for v in tri[1:]:
                b = find(int(v))
                if a != b:
                    parent[b] = a
        nb = len({find(i) for i in range(len(tm.vertices))})
    say(f"connected bodies={nb}  (must be 1 -- more means a feature is floating)")
    if nb > 1:
        bad.append(("disconnected geometry", -1))

    # EACH HALF has to be one body too, and that is a stricter test than the
    # whole part passing: the split can sever a boss from the material it
    # stands on, which is exactly what happened to the mic boss when the lap
    # ran through it. The whole part stays connected; the half does not.
    def bodies(solid):
        m = solid.to_mesh()
        vv, ff = m.vert_properties[:, :3], m.tri_verts
        par = list(range(len(vv)))

        def fnd(i):
            while par[i] != i:
                par[i] = par[par[i]]
                i = par[i]
            return i

        for tri in ff:
            a = fnd(int(tri[0]))
            for v in tri[1:]:
                b = fnd(int(v))
                if a != b:
                    par[b] = a
        return len({fnd(i) for i in range(len(vv))})

    if NEEDS_SPLIT:
        for _nm, _p in (("front-module-L", left_part),
                        ("front-module-R", right_part)):
            _n = bodies(_p)
            say(f"  {'FAIL' if _n != 1 else 'ok  '}  {_nm}.stl  bodies={_n}")
            if _n != 1:
                bad.append((f"{_nm} disconnected", -1))
except Exception as e:
    say(f"validate skipped: {e}")

say("")
say("ALL CLEAR" if not bad else f"*** {len(bad)} PROBLEM(S) ***")


# ---------------------------------------------------------------------------
# PREVIEW -- shaded views from the back (where all the features are) and the
# front, plus plan slices at each z level that matters.
# ---------------------------------------------------------------------------
def preview():
    import matplotlib
    matplotlib.use("Agg")
    import matplotlib.pyplot as plt
    import numpy as np
    from mpl_toolkits.mplot3d.art3d import Poly3DCollection

    out = os.environ.get("PREVIEW_DIR", base)
    v, f = np.asarray(V, dtype=float), np.asarray(F)
    tri = v[f]

    # flat shading against a fixed light
    nrm = np.cross(tri[:, 1] - tri[:, 0], tri[:, 2] - tri[:, 0])
    nl = np.linalg.norm(nrm, axis=1)
    nrm = np.nan_to_num(nrm / np.where(nl < 1e-12, 1.0, nl)[:, None])

    fig = plt.figure(figsize=(17, 7.2))
    views = [("from the BACK - clips, posts, ribs, cavity wall", 34, -122),
             ("from the FRONT - the facade", 20, 62)]
    for k, (title, elev, azim) in enumerate(views):
        ax = fig.add_subplot(1, 2, k + 1, projection="3d")
        light = np.array([0.4, -0.7, 0.9])
        light = light / np.linalg.norm(light)
        with np.errstate(all="ignore"):
            sh = 0.32 + 0.68 * np.clip(np.nan_to_num(nrm) @ light, 0, 1)
        cols = np.stack([sh * 0.62, sh * 0.70, sh * 0.80, np.ones_like(sh)], 1)
        pc = Poly3DCollection(tri, facecolors=cols, edgecolors="none")
        ax.add_collection3d(pc)
        ax.set_title(title, fontsize=10)
        ax.view_init(elev=elev, azim=azim)
        ax.set_xlim(bb[0], bb[3])
        ax.set_ylim(bb[1], bb[4])
        ax.set_zlim(-90, 90)
        ax.set_box_aspect((bb[3]-bb[0], bb[4]-bb[1], 180))
        ax.set_axis_off()
    fig.tight_layout()
    fig.savefig(os.path.join(out, "front-module-3d.png"), dpi=104)
    plt.close(fig)

    # ---- plan slices, cut with a plain triangle/plane intersection so this
    # ---- does not need scipy
    levels = [(1.0, "facade: crescent + clock apertures, mic ports"),
              (3.0, "acrylic pocket, tray pocket, mic channel"),
              (5.5, "speaker ribs + posts, spine, cavity wall"),
              (9.0, "posts topped out, cavity + clips"),
              (16.0, "clip hooks about to close over the tray")]
    fig, axes = plt.subplots(len(levels), 1, figsize=(13, 2.5 * len(levels)))
    for ax, (z, name) in zip(axes, levels):
        segs = []
        d = tri[:, :, 2] - z
        for t, dd in zip(tri, d):
            s = np.sign(dd)
            if abs(s.sum()) == 3:
                continue
            pts = []
            for i in range(3):
                j = (i + 1) % 3
                if dd[i] == 0:
                    pts.append(t[i][:2])
                if dd[i] * dd[j] < 0:
                    u = dd[i] / (dd[i] - dd[j])
                    pts.append((t[i] + u * (t[j] - t[i]))[:2])
            if len(pts) >= 2:
                segs.append((pts[0], pts[1]))
        for p, q in segs:
            ax.plot([p[0], q[0]], [p[1], q[1]], "k", lw=0.55)
        ax.set_title(f"z = {z}   {name}", fontsize=9, loc="left")
        ax.set_aspect("equal")
        ax.set_xlim(bb[0] - 4, bb[3] + 4)
        ax.set_ylim(bb[1] - 4, bb[4] + 4)
        ax.tick_params(labelsize=6)
    fig.tight_layout()
    fig.savefig(os.path.join(out, "front-module-sections.png"), dpi=104)
    plt.close(fig)
    say("preview -> front-module-3d.png, front-module-sections.png")


try:
    preview()
except Exception as e:
    say(f"preview skipped: {e}")
