AStoker/sound-machine/3d-print/gen_dome.py

#!/usr/bin/env python3
"""DOME — PART 1. The shell: open front, open bottom, integral rear wall.

A "D" lying on its long flat side, extruded along the depth. It carries the joint
that the front module slides up into, the ledge and lugs the bottom plate screws
to, every rear-wall board and opening, and the crown controls.

    PRINT REAR WALL DOWN. That makes the rear wall the first layer -- a big flat
    face, and the one that carries the most features -- and every boss standing
    off it then grows straight up off the bed with no overhang at all. The side
    walls and the crown come out vertical.

>>> WHAT THAT ORIENTATION COSTS: anything projecting inward off a SIDE wall or
>>> off the CROWN is horizontal, i.e. an unsupported shelf. That is the four side
>>> lugs and the two crown board mounts. Every one of them gets a 45 deg gusset
>>> underneath -- see gusset(). Without them the slicer either bridges into space
>>> or fills the interior with support that has to be picked out of a shell you
>>> can barely reach into.

>>> NO SCREW ENTERS FROM OUTSIDE. Every boss here is BLIND: it stands proud of
>>> the INNER surface and its pilot stops short of the skin, so nothing shows on
>>> the outside of the machine. Screws go in from inside, towards the shell. The
>>> six that hold the bottom plate are the only fasteners you can see, and they
>>> are on the underside.
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
